nio101/MUTA_units/src/18F27J53_op_basecamp/dev_18F27J53_operator_basecamp.X/src/miwi/drv_mrf_miwi_89xa.h

/********************************************************************
 Software License Agreement:

 The software supplied herewith by Microchip Technology Incorporated
 (the "Company") for its PIC(R) Microcontroller is intended and
 supplied to you, the Company's customer, for use solely and
 exclusively on Microchip PIC Microcontroller products. The
 software is owned by the Company and/or its supplier, and is
 protected under applicable copyright laws. All rights are reserved.
 Any use in violation of the foregoing restrictions may subject the
 user to criminal sanctions under applicable laws, as well as to
 civil liability for the breach of the terms and conditions of this
 license.

 THIS SOFTWARE IS PROVIDED IN AN "AS IS" CONDITION. NO WARRANTIES,
 WHETHER EXPRESS, IMPLIED OR STATUTORY, INCLUDING, BUT NOT LIMITED
 TO, IMPLIED WARRANTIES OF MERCHANTABILITY AND FITNESS FOR A
 PARTICULAR PURPOSE APPLY TO THIS SOFTWARE. THE COMPANY SHALL NOT,
 IN ANY CIRCUMSTANCES, BE LIABLE FOR SPECIAL, INCIDENTAL OR
 CONSEQUENTIAL DAMAGES, FOR ANY REASON WHATSOEVER.
 *******************************************************************/
#ifndef _DRV_89XA_H_
#define _DRV_89XA_H_

#include "18F27J53/system.h"
#include "18F27J53/system_config.h"
#include "miwi/drv_mrf_miwi.h"
#include "miwi/drv_mrf_miwi_security.h"
#include "miwi/miwi_api.h"

/********************************************************************
MRF89XA Operating modes
**********************************************************************/
#define RF_SLEEP        0x00
#define RF_STANDBY      0x20
#define RF_SYNTHESIZER  0x40
#define RF_RECEIVER     0x60
#define RF_TRANSMITTER  0x80

#define CHIPMODE_SLEEPMODE 0x00	//000 [7:5]
#define CHIPMODE_STBYMODE  0x20	//001 ;default
#define CHIPMODE_FSMODE    0x40	//010
#define CHIPMODE_RX        0x60	//011
#define CHIPMODE_TX        0x80	//100

#define BITRATE_200     0x00
#define BITRATE_100     0x01
#define BITRATE_66      0x02
#define BITRATE_50      0x03
#define BITRATE_40      0x04
#define BITRATE_25      0x07
#define BITRATE_20      0x09
#define BITRATE_10      0x13
#define BITRATE_5       0x27
#define BITRATE_2       0x63

#define FREQBAND_902    0x00   //902-915 00 [4:3]
#define FREQBAND_915    0x08   //915-928 01 ;default
#define FREQBAND_863    0x10	//950-960 or 863-870 10

#define BW_25  0x00
#define BW_50  0x01
#define BW_75  0x02
#define BW_100 0x03
#define BW_125 0x04
#define BW_150 0x05
#define BW_175 0x06
#define BW_200 0x07
#define BW_225 0x08
#define BW_250 0x09
#define BW_275 0x0A
#define BW_300 0x0B
#define BW_325 0x0C
#define BW_350 0x0D
#define BW_375 0x0E
#define BW_400 0x0F

#define FREQ_DEV_33  0x0B
#define FREQ_DEV_40  0x09
#define FREQ_DEV_50  0x07
#define FREQ_DEV_67  0x05
#define FREQ_DEV_80  0x04
#define FREQ_DEV_100 0x03
#define FREQ_DEV_133 0x02
#define FREQ_DEV_200 0x01

#define VCO_TRIM_00 0x00            // [2:1] Vtune determined by tank inductor values
#define VCO_TRIM_01 0x02
#define VCO_TRIM_10 0x04
#define VCO_TRIM_11 0x06


#define LNA_GAIN_0_DB   0x00        //00 [1:0] 0dB ;default (This is IF Filter gain)
#define LNA_GAIN_45_DB  0x01        //01 -4.5dB
#define LNA_GAIN_9_DB   0x02        //10 -9dB
#define LNA_GAIN_135_DB 0x03        //11 -13.5dB

#define TX_POWER_13_DB      0x00    //[3:1], 13dBm
#define TX_POWER_10_DB      0x01	//10dBm
#define TX_POWER_7_DB       0x02	//7dBm
#define TX_POWER_4_DB       0x03	//4dBm
#define TX_POWER_1_DB       0x04	//1dBm
#define TX_POWER_N_2_DB     0x05	//-2dBm
#define TX_POWER_N_5_DB     0x06	//-5dBm
#define TX_POWER_N_8_DB     0x07	//-8dBm

#define FILCON_SET_65   0x00		//65 KHz
#define FILCON_SET_82   0x10		//82 KHz
#define FILCON_SET_109  0x20
#define FILCON_SET_137  0x30
#define FILCON_SET_157  0x40
#define FILCON_SET_184  0x50
#define FILCON_SET_211  0x60
#define FILCON_SET_234  0x70
#define FILCON_SET_262  0x80
#define FILCON_SET_321  0x90
#define FILCON_SET_378  0xA0
#define FILCON_SET_414  0xB0
#define FILCON_SET_458  0xC0
#define FILCON_SET_514  0xD0
#define FILCON_SET_676  0xE0
#define FILCON_SET_987  0xF0

#if defined(BAND_863)
    #define FREQ_BAND   FREQBAND_863        // 863-870 MHz or 950-960 MHz
    #if defined(APPLICATION_CIRCUIT_950)
        #define START_FREQUENCY 950000
    #else
        #define START_FREQUENCY 860000      //in KHz
    #endif
    #define R1CNT   125
    #define P1CNT	100
    #define S1CNT	20                      //center frequency - 868MHz
#elif defined(BAND_902)
    #define FREQ_BAND FREQBAND_902          // 902MHz
    #define	START_FREQUENCY 902000
    #define	R1CNT   119
    #define	P1CNT   99
    #define	S1CNT   25                        //center freq - 903MHz
#elif defined(BAND_915)
    #define FREQ_BAND   FREQBAND_915        // 915MHz
    #define	START_FREQUENCY 915000
    #define	R1CNT   119
    #define	P1CNT	100
    #define	S1CNT	50                      //center frequency - 916MHz
#else
    #error  "No valid frequency band defined"
#endif

//Define the R, P, S sets for different channels
#define	RVALUE  100

#if defined(BAND_863)
    #if(!defined(DATA_RATE_100) && !defined(DATA_RATE_200))
        #define	CHANNEL_SPACING	 300					//Channel spacing 300KHz (except for data rates 100 and 200kbps)
        #define CHANNEL_NUM 32
        #define FULL_CHANNEL_MAP 0xFFFFFFFF
    #else
        #define	CHANNEL_SPACING	384					//To support 25 channels instead of 32
        #define CHANNEL_NUM 25
        #define FULL_CHANNEL_MAP 0x01FFFFFF
    #endif
#else
    #define	CHANNEL_SPACING	 400					//Channel spacing 400KHz
    #define CHANNEL_NUM 32
    #define FULL_CHANNEL_MAP 0xFFFFFFFF
#endif

#define	FXTAL					12.8					//Frequency of the crystal in MHz

#define CHANNEL1_FREQ ((uint32_t)(START_FREQUENCY)+ CHANNEL_SPACING)
#define CHANNEL2_FREQ ((uint32_t)(START_FREQUENCY)+ (2*CHANNEL_SPACING))
#define CHANNEL3_FREQ ((uint32_t)(START_FREQUENCY)+ (3*CHANNEL_SPACING))
#define CHANNEL4_FREQ ((uint32_t)(START_FREQUENCY)+ (4*CHANNEL_SPACING))
#define CHANNEL5_FREQ ((uint32_t)(START_FREQUENCY)+ (5*CHANNEL_SPACING))
#define CHANNEL6_FREQ ((uint32_t)(START_FREQUENCY)+ (6*CHANNEL_SPACING))
#define CHANNEL7_FREQ ((uint32_t)(START_FREQUENCY)+ (7*CHANNEL_SPACING))
#define CHANNEL8_FREQ ((uint32_t)(START_FREQUENCY)+ (8*CHANNEL_SPACING))
#define CHANNEL9_FREQ ((uint32_t)(START_FREQUENCY)+ (9*CHANNEL_SPACING))
#define CHANNEL10_FREQ ((uint32_t)(START_FREQUENCY)+ (10*CHANNEL_SPACING))
#define CHANNEL11_FREQ ((uint32_t)(START_FREQUENCY)+ (11*CHANNEL_SPACING))
#define CHANNEL12_FREQ ((uint32_t)(START_FREQUENCY)+ (12*CHANNEL_SPACING))
#define CHANNEL13_FREQ ((uint32_t)(START_FREQUENCY)+ (13*CHANNEL_SPACING))
#define CHANNEL14_FREQ ((uint32_t)(START_FREQUENCY)+ (14*CHANNEL_SPACING))
#define CHANNEL15_FREQ ((uint32_t)(START_FREQUENCY)+ (15*CHANNEL_SPACING))
#define CHANNEL16_FREQ ((uint32_t)(START_FREQUENCY)+ (16*CHANNEL_SPACING))
#define CHANNEL17_FREQ ((uint32_t)(START_FREQUENCY)+ (17*CHANNEL_SPACING))
#define CHANNEL18_FREQ ((uint32_t)(START_FREQUENCY)+ (18*CHANNEL_SPACING))
#define CHANNEL19_FREQ ((uint32_t)(START_FREQUENCY)+ (19*CHANNEL_SPACING))
#define CHANNEL20_FREQ ((uint32_t)(START_FREQUENCY)+ (20*CHANNEL_SPACING))
#define CHANNEL21_FREQ ((uint32_t)(START_FREQUENCY)+ (21*CHANNEL_SPACING))
#define CHANNEL22_FREQ ((uint32_t)(START_FREQUENCY)+ (22*CHANNEL_SPACING))
#define CHANNEL23_FREQ ((uint32_t)(START_FREQUENCY)+ (23*CHANNEL_SPACING))
#define CHANNEL24_FREQ ((uint32_t)(START_FREQUENCY)+ (24*CHANNEL_SPACING))
#define CHANNEL25_FREQ ((uint32_t)(START_FREQUENCY)+ (25*CHANNEL_SPACING))
#define CHANNEL26_FREQ ((uint32_t)(START_FREQUENCY)+ (26*CHANNEL_SPACING))
#define CHANNEL27_FREQ ((uint32_t)(START_FREQUENCY)+ (27*CHANNEL_SPACING))
#define CHANNEL28_FREQ ((uint32_t)(START_FREQUENCY)+ (28*CHANNEL_SPACING))
#define CHANNEL29_FREQ ((uint32_t)(START_FREQUENCY)+ (29*CHANNEL_SPACING))
#define CHANNEL30_FREQ ((uint32_t)(START_FREQUENCY)+ (30*CHANNEL_SPACING))
#define CHANNEL31_FREQ ((uint32_t)(START_FREQUENCY)+ (31*CHANNEL_SPACING))
#define CHANNEL32_FREQ ((uint32_t)(START_FREQUENCY)+ (32*CHANNEL_SPACING))

#define CHANNEL1_COMPARE    (uint16_t)((uint32_t)(CHANNEL1_FREQ * 8 * 101)/(uint32_t)(9*FXTAL*1000))
#define CHANNEL2_COMPARE    (uint16_t)((uint32_t)(CHANNEL2_FREQ * 8 * 101)/(uint32_t)(9*FXTAL*1000))
#define CHANNEL3_COMPARE    (uint16_t)((uint32_t)(CHANNEL3_FREQ * 8 * 101)/(uint32_t)(9*FXTAL*1000))
#define CHANNEL4_COMPARE    (uint16_t)((uint32_t)(CHANNEL4_FREQ * 8 * 101)/(uint32_t)(9*FXTAL*1000))
#define CHANNEL5_COMPARE    (uint16_t)((uint32_t)(CHANNEL5_FREQ * 8 * 101)/(uint32_t)(9*FXTAL*1000))
#define CHANNEL6_COMPARE    (uint16_t)((uint32_t)(CHANNEL6_FREQ * 8 * 101)/(uint32_t)(9*FXTAL*1000))
#define CHANNEL7_COMPARE    (uint16_t)((uint32_t)(CHANNEL7_FREQ * 8 * 101)/(uint32_t)(9*FXTAL*1000))
#define CHANNEL8_COMPARE    (uint16_t)((uint32_t)(CHANNEL8_FREQ * 8 * 101)/(uint32_t)(9*FXTAL*1000))
#define CHANNEL9_COMPARE    (uint16_t)((uint32_t)(CHANNEL9_FREQ * 8 * 101)/(uint32_t)(9*FXTAL*1000))
#define CHANNEL10_COMPARE   (uint16_t)((uint32_t)(CHANNEL10_FREQ * 8 * 101)/(uint32_t)(9*FXTAL*1000))
#define CHANNEL11_COMPARE   (uint16_t)((uint32_t)(CHANNEL11_FREQ * 8 * 101)/(uint32_t)(9*FXTAL*1000))
#define CHANNEL12_COMPARE   (uint16_t)((uint32_t)(CHANNEL12_FREQ * 8 * 101)/(uint32_t)(9*FXTAL*1000))
#define CHANNEL13_COMPARE   (uint16_t)((uint32_t)(CHANNEL13_FREQ * 8 * 101)/(uint32_t)(9*FXTAL*1000))
#define CHANNEL14_COMPARE   (uint16_t)((uint32_t)(CHANNEL14_FREQ * 8 * 101)/(uint32_t)(9*FXTAL*1000))
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
#define CHANNEL26_SVALUE    (uint8_t)(((uint16_t)CHANNEL26_COMPARE - ((uint16_t)(75*(CHANNEL26_PVALUE+1)))))
#define CHANNEL27_SVALUE    (uint8_t)(((uint16_t)CHANNEL27_COMPARE - ((uint16_t)(75*(CHANNEL27_PVALUE+1)))))
#define CHANNEL28_SVALUE    (uint8_t)(((uint16_t)CHANNEL28_COMPARE - ((uint16_t)(75*(CHANNEL28_PVALUE+1)))))
#define CHANNEL29_SVALUE    (uint8_t)(((uint16_t)CHANNEL29_COMPARE - ((uint16_t)(75*(CHANNEL29_PVALUE+1)))))
#define CHANNEL30_SVALUE    (uint8_t)(((uint16_t)CHANNEL30_COMPARE - ((uint16_t)(75*(CHANNEL30_PVALUE+1)))))
#define CHANNEL31_SVALUE    (uint8_t)(((uint16_t)CHANNEL31_COMPARE - ((uint16_t)(75*(CHANNEL31_PVALUE+1)))))
#define CHANNEL32_SVALUE    (uint8_t)(((uint16_t)CHANNEL32_COMPARE - ((uint16_t)(75*(CHANNEL32_PVALUE+1)))))

#if defined(DATA_RATE_2)
    #define         DATARATE                 BITRATE_2
    #define			BANDWIDTH				 BW_50
    #define 		FREQ_DEV				 FREQ_DEV_33
    #define			FILCON_SET				 FILCON_SET_157
#elif defined(DATA_RATE_5)
    #define         DATARATE                 BITRATE_5
    #define			BANDWIDTH				 BW_50
    #define 		FREQ_DEV				 FREQ_DEV_33
    #define			FILCON_SET				 FILCON_SET_157
#elif defined(DATA_RATE_10)
    #define         DATARATE                 BITRATE_10
    #define			BANDWIDTH				 BW_50
    #define 		FREQ_DEV				 FREQ_DEV_33
    #define			FILCON_SET				 FILCON_SET_157
#elif defined(DATA_RATE_20)
    #define         DATARATE                 BITRATE_20
    #define			BANDWIDTH				 BW_75
    #define 		FREQ_DEV				 FREQ_DEV_40
    #define			FILCON_SET				 FILCON_SET_234
#elif defined(DATA_RATE_40)
    #define         DATARATE                 BITRATE_40
    #define			BANDWIDTH				 BW_150
    #define 		FREQ_DEV				 FREQ_DEV_80
    #define			FILCON_SET				 FILCON_SET_414
#elif defined(DATA_RATE_50)
    #define         DATARATE                 BITRATE_50
    #define			BANDWIDTH				 BW_175
    #define 		FREQ_DEV				 FREQ_DEV_100
    #define			FILCON_SET				 FILCON_SET_514
#elif defined(DATA_RATE_66)
    #define         DATARATE                 BITRATE_66
    #define			BANDWIDTH				 BW_250
    #define 		FREQ_DEV				 FREQ_DEV_133
    #define			FILCON_SET				 FILCON_SET_676
#elif defined(DATA_RATE_100)
    #define         DATARATE                 BITRATE_100
    #define			BANDWIDTH				 BW_400
    #define 		FREQ_DEV				 FREQ_DEV_200
    #define			FILCON_SET				 FILCON_SET_987
#elif defined(DATA_RATE_200)
    #define         DATARATE                 BITRATE_200
    #define			BANDWIDTH				 BW_400
    #define 		FREQ_DEV				 FREQ_DEV_200
    #define			FILCON_SET				 FILCON_SET_987
#endif

    //default register settings
#define GCONREG_SET     (CHIPMODE_STBYMODE | FREQ_BAND | VCO_TRIM_11)
#define DMODREG_SET     (0x84 | LNA_GAIN)
#define FLTHREG_SET     (0x0C)
#define FIFOCREG_SET    (0xC1)								//FIFO size = 64 bytes and threshold limit for IRQ is 1
#define PACONREG_SET    (0x38)
#define FTXRXIREG_SET   (0xC8)
#define FTPRIREG_SET    (0x0D)
#define RSTHIREG_SET    (0x00)	
#define FILCONREG_SET   (FILCON_SET | BANDWIDTH)
#define PFILCREG_SET    (0x38)
#define SYNCREG_SET     (0x38)
#define RESVREG_SET     (0x07)
#define SYNCV31REG_SET  (0x69)
#define SYNCV23REG_SET  (0x81)
#define SYNCV15REG_SET  (0x7E)
#define SYNCV07REG_SET  (0x96)
#define TXPARAMREG_SET  (0xF0 | (TX_POWER<<1))
#define CLKOUTREG_SET   (0x88)
#define PLOADREG_SET    (0x40)
#define NADDREG_SET     (0x00)
#define PCONREG_SET     (0xE8)
#define FCRCREG_SET     (0x00)

            //register description
#define GCONREG     0x0000
#define DMODREG     0x0200
#define FDEVREG     0x0400
#define BRREG       0x0600
#define FLTHREG     0x0800
#define FIFOCREG    0x0A00	
#define R1CNTREG    0x0C00
#define P1CNTREG    0x0E00
#define S1CNTREG    0x1000
#define R2CNTREG    0x1200
#define P2CNTREG    0x1400
#define S2CNTREG    0x1600
#define PACONREG    0x1800
#define FTXRXIREG   0x1A00
#define FTPRIREG    0x1C00
#define RSTHIREG    0x1E00
#define FILCONREG   0x2000
#define PFILCREG    0x2200
#define SYNCREG     0x2400
#define RESVREG     0x2600
#define RSTSREG     0x2800
#define OOKCREG     0x2A00
#define SYNCV31REG  0x2C00
#define SYNCV23REG  0x2E00
#define SYNCV15REG  0x3000
#define SYNCV07REG  0x3200
#define TXPARAMREG  0x3400
#define CLKOUTREG   0x3600
#define PLOADREG    0x3800
#define NADDREG     0x3A00
#define PCONREG     0x3C00
#define FCRCREG     0x3E00

#if defined(PROTOCOL_MIWI)
    #define PROTOCOL_HEADER_SIZE 11
#endif

#if defined(PROTOCOL_MIWI_PRO)
    #define PROTOCOL_HEADER_SIZE 11
#endif

#if defined(PROTOCOL_P2P)
    #define PROTOCOL_HEADER_SIZE 0
#endif

#if defined(ENABLE_SECURITY)
    #define TX_PACKET_SIZE (TX_BUFFER_SIZE+PROTOCOL_HEADER_SIZE+BLOCK_SIZE+MY_ADDRESS_LENGTH+MY_ADDRESS_LENGTH+9)
    #define RX_PACKET_SIZE (RX_BUFFER_SIZE+PROTOCOL_HEADER_SIZE+MY_ADDRESS_LENGTH+MY_ADDRESS_LENGTH+BLOCK_SIZE+9)
#else
    #define TX_PACKET_SIZE  (TX_BUFFER_SIZE+PROTOCOL_HEADER_SIZE+MY_ADDRESS_LENGTH+MY_ADDRESS_LENGTH+4)
    #define RX_PACKET_SIZE  (RX_BUFFER_SIZE+PROTOCOL_HEADER_SIZE+MY_ADDRESS_LENGTH+MY_ADDRESS_LENGTH+4)
#endif

#if RX_PACKET_SIZE > 64
    #warning  "Maximum RX PACKET SIZE should not be greater 64, redefine RX BUFFER SIZE"
    #undef RX_PACKET_SIZE
    #define RX_PACKET_SIZE 64
#endif

#if TX_PACKET_SIZE > 64
    #warning  "Maximum TX PACKET SIZE should not be greater 64, redefine TX BUFFER SIZE"
    #undef TX_PACKET_SIZE
    #define TX_PACKET_SIZE 64
#endif

typedef struct
{
    union
    {
        uint8_t    Val;
        struct
        {
            uint8_t    Valid       :1;
        } bits;
    } flags;
    uint8_t        Payload[RX_PACKET_SIZE];
    uint8_t        PayloadLen;
} RX_PACKET;

typedef struct
{
    bool        Valid;
    uint8_t        Seq;
    MIWI_TICK   startTick;
} ACK_INFO;

void MIWIInterruptHandler(void);

#endif
