nio101/MUTA_units/src/18F27J53_op_basecamp/dev_18F27J53_operator_basecamp.X/src/miwi/miwi_mesh.c

/********************************************************************
Software License Agreement:

The software supplied herewith by Microchip Technology Incorporated
(the "Company") for its PIC(R) Microcontroller is intended and
supplied to you, the Company's customer, for use solely and
exclusively on Microchip PIC Microcontroller products. The
software is owned by the Company and/or its supplier, and is
protected under applicable copyright laws. All rights are reserved.
Any use in violation of the foregoing restrictions may subject the
user to criminal sanctions under applicable laws, as well as to
civil liability for the breach of the terms and conditions of this
license.

THIS SOFTWARE IS PROVIDED IN AN "AS IS" CONDITION. NO WARRANTIES,
WHETHER EXPRESS, IMPLIED OR STATUTORY, INCLUDING, BUT NOT LIMITED
TO, IMPLIED WARRANTIES OF MERCHANTABILITY AND FITNESS FOR A
PARTICULAR PURPOSE APPLY TO THIS SOFTWARE. THE COMPANY SHALL NOT,
IN ANY CIRCUMSTANCES, BE LIABLE FOR SPECIAL, INCIDENTAL OR
CONSEQUENTIAL DAMAGES, FOR ANY REASON WHATSOEVER.
*******************************************************************/

/************************ HEADERS **********************************/

#include "system.h"
#include "system_config.h"


#include "drv_mrf_miwi.h"
#include "miwi_mesh.h"
//#include "miwi_nvm.h"
#include "miwi_api.h"

/************************ VARIABLES ********************************/

// Scan Duration formula 
//  60 * (2 ^ n + 1) symbols, where one symbol equals 16us
#define SCAN_DURATION_0 SYMBOLS_TO_TICKS(120)
#define SCAN_DURATION_1 SYMBOLS_TO_TICKS(180)
#define SCAN_DURATION_2 SYMBOLS_TO_TICKS(300)
#define SCAN_DURATION_3 SYMBOLS_TO_TICKS(540)
#define SCAN_DURATION_4 SYMBOLS_TO_TICKS(1020)
#define SCAN_DURATION_5 SYMBOLS_TO_TICKS(1980)
#define SCAN_DURATION_6 SYMBOLS_TO_TICKS(3900)
#define SCAN_DURATION_7 SYMBOLS_TO_TICKS(7740)
#define SCAN_DURATION_8 SYMBOLS_TO_TICKS(15420)
#define SCAN_DURATION_9 SYMBOLS_TO_TICKS(30780)
#define SCAN_DURATION_10 SYMBOLS_TO_TICKS(61500)
#define SCAN_DURATION_11 SYMBOLS_TO_TICKS(122940)
#define SCAN_DURATION_12 SYMBOLS_TO_TICKS(245820)
#define SCAN_DURATION_13 SYMBOLS_TO_TICKS(491580)
#define SCAN_DURATION_14 SYMBOLS_TO_TICKS(983100)
const uint32_t ScanTime[15] = {SCAN_DURATION_0,SCAN_DURATION_1,SCAN_DURATION_2,SCAN_DURATION_3,
    SCAN_DURATION_4,SCAN_DURATION_5,SCAN_DURATION_6,SCAN_DURATION_7,SCAN_DURATION_8,SCAN_DURATION_9,
    SCAN_DURATION_10, SCAN_DURATION_11, SCAN_DURATION_12, SCAN_DURATION_13,SCAN_DURATION_14
};

// permanent address definition

// MY_ADDRESS_LENGTH == 4 (always)
// and we're using the myMODEL and myUID identifiers
// as unique long address
//uint8_t myLongAddress[4] @ 0x01FFF4;
uint8_t myLongAddress[4];

/*
#if MY_ADDRESS_LENGTH == 8
    uint8_t myLongAddress[MY_ADDRESS_LENGTH] = {EUI_0,EUI_1,EUI_2,EUI_3, EUI_4, EUI_5,EUI_6,EUI_7};
#elif MY_ADDRESS_LENGTH == 7
    uint8_t myLongAddress[MY_ADDRESS_LENGTH] = {EUI_0,EUI_1,EUI_2,EUI_3, EUI_4, EUI_5,EUI_6};
#elif MY_ADDRESS_LENGTH == 6
    uint8_t myLongAddress[MY_ADDRESS_LENGTH] = {EUI_0,EUI_1,EUI_2,EUI_3, EUI_4, EUI_5};
#elif MY_ADDRESS_LENGTH == 5
    uint8_t myLongAddress[MY_ADDRESS_LENGTH] = {EUI_0,EUI_1,EUI_2,EUI_3, EUI_4};
#elif MY_ADDRESS_LENGTH == 4
    uint8_t myLongAddress[MY_ADDRESS_LENGTH] = {EUI_0,EUI_1,EUI_2,EUI_3};
#elif MY_ADDRESS_LENGTH == 3
    uint8_t myLongAddress[MY_ADDRESS_LENGTH] = {EUI_0,EUI_1,EUI_2};
#elif MY_ADDRESS_LENGTH == 2
    uint8_t myLongAddress[MY_ADDRESS_LENGTH] = {EUI_0,EUI_1};
#endif
 */

uint8_t            currentChannel = 0;             // current operating channel for the device
uint8_t            ConnMode = 0;
typedef union
{
    uint8_t        Val;
    struct
    {
        uint8_t    Sleep           :1;
        uint8_t    Role            :2;
        uint8_t    Security        :1;
        uint8_t    ConnMode        :2;
        uint8_t    CoordCap        :1;
    }bits;
} MIWI_CAPACITY_INFO;    
MIWI_CAPACITY_INFO MiWiCapacityInfo;        
RECEIVED_MESSAGE  rxMessage;                    // structure to store information for the received packet
extern uint8_t     AdditionalNodeID[];             // the additional information regarding the device
                                                // that would like to share with the peer on the
                                                // other side of P2P connection. This information
                                                // is applicaiton specific.

uint8_t    ActiveScanResultIndex;
ACTIVE_SCAN_RESULT ActiveScanResults[ACTIVE_SCAN_RESULT_SIZE];  // The results for active scan, including
                                                                // the PAN identifier, signal strength and
                                                                // operating channel

#ifdef ENABLE_SLEEP
    MIWI_TICK DataRequestTimer;
#endif

uint8_t tempLongAddress[MY_ADDRESS_LENGTH];
API_UINT16_UNION tempShortAddress;
API_UINT16_UNION tempPANID;
CONNECTION_STATUS tempNodeStatus;

uint8_t            TxData;

#if (TX_BUFFER_SIZE+MIWI_HEADER_LEN) > 110
    uint8_t TxBuffer[110];
#else
    uint8_t TxBuffer[TX_BUFFER_SIZE+MIWI_HEADER_LEN];
#endif
#if defined(ENABLE_SECURITY)
    API_UINT32_UNION IncomingFrameCounter[CONNECTION_SIZE];
#endif

API_UINT16_UNION myShortAddress;
API_UINT16_UNION myPANID;
uint8_t myParent;
uint8_t defaultHops = MAX_HOPS;

MIWI_STATE_MACHINE MiWiStateMachine;
uint8_t AcknowledgementSeq = 0xFF;
API_UINT16_UNION AcknowledgementAddr;
uint8_t MiWiSeqNum;
#if defined(ENABLE_MIWI_ACKNOWLEDGEMENT)
    bool MiWiAckRequired = true;
#else
    bool MiWiAckRequired = false;
#endif

#ifdef NWK_ROLE_COORDINATOR
    #if defined(ENABLE_INDIRECT_MESSAGE)
        #if defined(__18CXX)
            #pragma udata INDIRECT_BUFFER
        #endif
        INDIRECT_MESSAGE indirectMessages[INDIRECT_MESSAGE_SIZE];
        #if defined(__18CXX)
            #pragma udata
        #endif
    #endif
    uint8_t RoutingTable[8];
    uint8_t RouterFailures[8];
    uint8_t knownCoordinators;
    uint8_t role;
#endif

OPEN_SOCKET openSocketInfo;

MAC_TRANS_PARAM MTP;
MAC_RECEIVED_PACKET MACRxPacket;


CONNECTION_ENTRY    ConnectionTable[CONNECTION_SIZE]; 


struct _BROADCAST_RECORD
{
    API_UINT16_UNION    AltSourceAddr;
    uint8_t             MiWiSeq;
    uint8_t             RxCounter;
    MIWI_TICK           StartTick;
} BroadcastRecords[BROADCAST_RECORD_SIZE];

#if defined(ENABLE_NETWORK_FREEZER)
    MIWI_TICK nvmDelayTick;
#endif 

#if defined(ENABLE_TIME_SYNC)
    #if defined(ENABLE_SLEEP)
        API_UINT16_UNION WakeupTimes;
        API_UINT16_UNION CounterValue;
    #elif defined(ENABLE_INDIRECT_MESSAGE)
        uint8_t        TimeSyncSlot = 0;
        MIWI_TICK   TimeSyncTick;
        MIWI_TICK   TimeSlotTick;
    #endif
#endif
/************************ FUNCTIONS ********************************/

#if defined(IEEE_802_15_4)
    bool SendMACPacket(uint8_t *PANID, uint8_t *Address, uint8_t PacketType, uint8_t ModeMask);
#else
    bool SendMACPacket(uint8_t *Address, uint8_t PacketType);
#endif

bool RouteMessage(API_UINT16_UNION PANID, API_UINT16_UNION ShortAddress, bool SecEn);
void StartChannelHopping(INPUT uint8_t OptimalChannel);
void SendBeacon(void);

#if defined(IEEE_802_15_4)
    bool SaveIndirectMessage(INPUT bool Broadcast,
                             INPUT API_UINT16_UNION DestinationPANID,
                             INPUT uint8_t *DestinationAddress,
                             INPUT bool isAltAddr,
                             INPUT bool SecurityEnabled);
#else
    bool SaveIndirectMessage(INPUT bool Broadcast,
                             INPUT uint8_t *DestinationAddress,
                             INPUT bool isAltAddr,
                             INPUT bool SecurityEnabled);
#endif  

/******************************************************************/
// C18 compiler cannot optimize the code with a macro. Instead of 
// calling macro Nop in a big function, we define a wrapper to call
// Nop in order to be able to optimize the code efficiently.
/******************************************************************/
void MacroNop(void)
{
    Nop();
}   

#if !defined(TARGET_SMALL)
    /******************************************************************/
    // Function:        void BroadcastJitter(uint8_t range)
    //
    // PreCondition:    None
    //
    // Input:           range   - The range of random delay in milli
    //                            second.
    //
    // Output:          None
    //
    // Side Effect:     A random delay between 0 to range in milli
    //                  second
    //
    // Overview:        This function introduce a random delay between
    //                  0 to range in millisecond. This delay helps
    //                  multiple devices to rebroadcast the message
    //                  at different time, thus lower the possibility
    //                  of packet collision in rebroadcast.
    /******************************************************************/
    void BroadcastJitter(uint8_t range)
    {
        uint8_t jitter = TMR_L % range;
        MIWI_TICK t1, t2;

        while( jitter > 0 )
        {
            jitter--;
            t1 = MiWi_TickGet();
            while(1)
            {
                t2 = MiWi_TickGet();
                if( MiWi_TickGetDiff(t2, t1) > ONE_MILI_SECOND )
                {
                    break;
                }
            }
        }
    }
#endif

/*********************************************************************
 * Function:        void MiWiTasks( void )
 *
 * PreCondition:    None
 *
 * Input:           None
 *
 * Output:          None
 *
 * Side Effects:    The stack receives, handles, buffers, and transmits
 *                  packets.  It also handles all of the joining
 *
 * Overview:        This function maintains the operation of the stack
 *                  It should be called as often as possible.
 ********************************************************************/
void MiWiTasks(void)
{
    uint8_t i;
    MIWI_TICK t1, t2;

    if( MiMAC_ReceivedPacket() )
    {
        if( MiWiStateMachine.bits.RxHasUserData )
        {
            return;
        }

        rxMessage.flags.Val = 0;
        rxMessage.flags.bits.broadcast = MACRxPacket.flags.bits.broadcast;
        rxMessage.flags.bits.secEn = MACRxPacket.flags.bits.secEn;
        rxMessage.flags.bits.command = (MACRxPacket.flags.bits.packetType == PACKET_TYPE_COMMAND) ? 1:0;
        rxMessage.flags.bits.srcPrsnt = MACRxPacket.flags.bits.sourcePrsnt;
        if( MACRxPacket.flags.bits.sourcePrsnt )
        {
            #if defined(IEEE_802_15_4)
                rxMessage.flags.bits.altSrcAddr = MACRxPacket.altSourceAddress;
            #else
                rxMessage.flags.bits.altSrcAddr = 1;
            #endif
            rxMessage.SourceAddress = MACRxPacket.SourceAddress;
        }
        #if defined(IEEE_802_15_4)
            rxMessage.SourcePANID.Val = MACRxPacket.SourcePANID.Val;
        #endif
        rxMessage.PacketLQI = MACRxPacket.LQIValue;
        rxMessage.PacketRSSI = MACRxPacket.RSSIValue;

        MiWiStateMachine.bits.RxHasUserData = 0;

        //determine what type of packet it is.
        switch(MACRxPacket.flags.bits.packetType)
        {
            //if it is a data packet
            case PACKET_TYPE_DATA:
                //The guts of MiWi ...
                {
                    API_UINT16_UNION destPANID;
                    API_UINT16_UNION sourcePANID;
                    API_UINT16_UNION sourceShortAddress;
                    API_UINT16_UNION destShortAddress;
HANDLE_DATA_PACKET:  
                    #if defined(ENABLE_SLEEP)
                        #if defined(ENABLE_BROADCAST_TO_SLEEP_DEVICE)
                            for(i = 0; i < BROADCAST_RECORD_SIZE; i++)
                            {
                                if( BroadcastRecords[i].RxCounter > 0)
                                {
                                    BroadcastRecords[i].RxCounter--;
                                }
                            }
                        #endif

                        // If it is just an empty packet, ignore here.
                        if( MACRxPacket.PayloadLen == 0 )
                        {
                            MiWiStateMachine.bits.DataRequesting = 0;
                            break;
                        }
                    #endif

                    if( MACRxPacket.PayloadLen < 10 )
                    {
                        break;
                    }

                    // Load the source and destination address information.
                    destPANID.v[0] = MACRxPacket.Payload[2];
                    destPANID.v[1] = MACRxPacket.Payload[3];
                    destShortAddress.v[0] = MACRxPacket.Payload[4];
                    destShortAddress.v[1] = MACRxPacket.Payload[5];
                    sourcePANID.v[0] = MACRxPacket.Payload[6];
                    sourcePANID.v[1] = MACRxPacket.Payload[7];
                    sourceShortAddress.v[0] = MACRxPacket.Payload[8];
                    sourceShortAddress.v[1] = MACRxPacket.Payload[9];

                    rxMessage.flags.Val = 0;
                    rxMessage.flags.bits.secEn = MACRxPacket.flags.bits.secEn;
                    // if this is a broadcast
                    if(rxMessage.flags.bits.broadcast || destShortAddress.Val == 0xFFFF)
                    {
                        // if this broadcast is from myself
                        if( sourceShortAddress.Val == myShortAddress.Val &&
                            sourcePANID.Val == myPANID.Val )
                        {
                            break;
                        }

                        #ifdef NWK_ROLE_COORDINATOR
                            // Consider to rebroadcast the message
                            if(MACRxPacket.Payload[0]>1)
                            {
                                MACRxPacket.Payload[0]--;
                                MAC_FlushTx();
                                for(i = 0; i < MACRxPacket.PayloadLen; i++)
                                {
                                    MiApp_WriteData(MACRxPacket.Payload[i]);
                                }

                                MTP.flags.Val = MACRxPacket.flags.Val;
                                #if defined(IEEE_802_15_4)
                                    MTP.DestPANID.Val = myPANID.Val;
                                    MTP.altSrcAddr = MACRxPacket.altSourceAddress;
                                #endif

                                #if !defined(TARGET_SMALL)
                                    // introduce a random delay to avoid rebroadcast at
                                    // the same time
                                    BroadcastJitter(20);
                                #endif

                                MiMAC_SendPacket(MTP, TxBuffer, TxData);
                                #if defined(ENABLE_INDIRECT_MESSAGE)
                                    for(i = 0; i < CONNECTION_SIZE; i++)
                                    {
                                        if( ConnectionTable[i].status.bits.isValid && (ConnectionTable[i].status.bits.RXOnWhenIdle == 0) &&
                                            ConnectionTable[i].status.bits.isFamily )
                                        {
                                            break;
                                        }
                                    }
                                    if( i < CONNECTION_SIZE )
                                    {
                                        #if defined(IEEE_802_15_4)
                                            SaveIndirectMessage(true, destPANID, NULL, false, MACRxPacket.flags.bits.secEn);
                                        #else
                                            SaveIndirectMessage(true, NULL, false, MACRxPacket.flags.bits.secEn);
                                        #endif
                                    }
                                #endif
                            }
                        #endif

                        //since this is a broadcast we need to parse the packet as well.
                        for(i = 0; i < BROADCAST_RECORD_SIZE; i++)
                        {
                            if( BroadcastRecords[i].RxCounter &&
                                BroadcastRecords[i].AltSourceAddr.Val == sourceShortAddress.Val &&
                                BroadcastRecords[i].MiWiSeq == MACRxPacket.Payload[10] )
                            {
                                break;
                            }
                        }

                        // if the broadcast is already in the broadcast record
                        if( i < BROADCAST_RECORD_SIZE )
                        {
                            #if defined(ENABLE_SLEEP)
                                MiWiStateMachine.bits.DataRequesting = 0;
                            #endif
                            break;
                        }


                        // save the broadcast information into the broadcast record.
                        for(i = 0; i < BROADCAST_RECORD_SIZE; i++)
                        {
                            if( BroadcastRecords[i].RxCounter == 0 )
                            {
                                break;
                            }
                        }

                        if( i < BROADCAST_RECORD_SIZE )
                        {
                            BroadcastRecords[i].AltSourceAddr.Val = sourceShortAddress.Val;
                            BroadcastRecords[i].MiWiSeq = MACRxPacket.Payload[10];
                            BroadcastRecords[i].RxCounter = INDIRECT_MESSAGE_TIMEOUT_CYCLE + 1;
                            #if !defined(ENABLE_SLEEP)
                                BroadcastRecords[i].StartTick = MiWi_TickGet();
                            #endif
                        }

                        rxMessage.flags.bits.broadcast = 1;
                        goto ThisPacketIsForMe;
                    }

                    // this is unicast
                    if((destPANID.Val == myPANID.Val) && (destShortAddress.Val == myShortAddress.Val))
                    {
                        //need to check to see if the MiWi Ack is set
                        if(MACRxPacket.Payload[1] & MIWI_ACK_REQ)
                        {
                            TxBuffer[0] = defaultHops;				//number of hops
                            TxBuffer[1] = 0x02;		            //Frame Control
                            TxBuffer[2] = sourcePANID.v[0];
                            TxBuffer[3] = sourcePANID.v[1];
                            TxBuffer[4] = sourceShortAddress.v[0];
                            TxBuffer[5] = sourceShortAddress.v[1];
                            TxBuffer[6] = myPANID.v[0];			//source PANID LSB
                            TxBuffer[7] = myPANID.v[1];			//source PANID MSB
                            TxBuffer[8] = myShortAddress.v[0];	//source address LSB
                            TxBuffer[9] = myShortAddress.v[1];	//source address MSB
                            TxBuffer[10] = MACRxPacket.Payload[MIWI_HEADER_LEN-1];   //sequence number
                            TxBuffer[11] = MIWI_STACK_REPORT_TYPE;
                            TxBuffer[12] = ACK_REPORT_TYPE;
                            TxData = 13;

                            #if defined(NWK_ROLE_COORDINATOR)
                                if( sourceShortAddress.v[1] != myShortAddress.v[1] )
                                {
                                    RouteMessage(sourcePANID, sourceShortAddress, false);
                                }
                                else
                                {
                                    MTP.flags.Val = 0;
                                    MTP.flags.bits.ackReq = 1;

                                    #if defined(IEEE_802_15_4)
                                        MTP.altDestAddr = true;
                                        MTP.altSrcAddr = true;
                                        MTP.DestAddress = sourceShortAddress.v;
                                        MTP.DestPANID.Val = sourcePANID.Val;
                                    #else
                                        tempShortAddress.Val = sourceShortAddress.Val;
                                        tempPANID.Val = sourcePANID.Val;
                                        if( (i = SearchForShortAddress()) != 0xFF )
                                        {
                                            MTP.DestAddress = ConnectionTable[i].Address;
                                        }
                                    #endif

                                    MiMAC_SendPacket(MTP, TxBuffer, TxData);
                                }
                            #else
                                // for end device, always send the message to its parent
                                MTP.flags.Val = 0;
                                MTP.flags.bits.ackReq = 1;

                                #if defined(IEEE_802_15_4)
                                    MTP.altDestAddr = true;
                                    MTP.altSrcAddr = true;
                                    MTP.DestAddress = ConnectionTable[myParent].AltAddress.v;
                                    MTP.DestPANID.Val = myPANID.Val;
                                #else
                                    MTP.DestAddress = ConnectionTable[myParent].Address;
                                #endif

                                MiMAC_SendPacket(MTP, TxBuffer, TxData);
                            #endif
                            rxMessage.flags.bits.ackReq = 1;
                        }

ThisPacketIsForMe:
                        //if the packet is a MiWi stack packet (but not an ACK report type
                        if(MACRxPacket.Payload[MIWI_HEADER_LEN] == MIWI_STACK_REPORT_TYPE)
                        {
                            if( MACRxPacket.Payload[MIWI_HEADER_LEN+1] != ACK_REPORT_TYPE)
                            {
                                //determine which stack report it was
                                switch(MACRxPacket.Payload[MIWI_HEADER_LEN+1])
                                {
                                    #if defined(SUPPORT_EUI_ADDRESS_SEARCH)
                                    #if defined(NWK_ROLE_COORDINATOR)
                                    case EUI_ADDRESS_SEARCH_REQUEST:
                                        {
                                            uint8_t handle,j;
                                            bool ItsMe;

                                            if(sourceShortAddress.Val == myShortAddress.Val)
                                            {
                                                if(sourcePANID.Val == myPANID.Val)
                                                {
                                                    //I started this message.  I don't need to re-broadcast it.
                                                    break;
                                                }
                                            }

                                            //copy the address into tempLongAddress
                                            CONSOLE_PutString((char*)"\r\nEUI address search request\r\n");
                                            for(j = 0; j < MY_ADDRESS_LENGTH; j++)
                                            {
                                                tempLongAddress[j] = MACRxPacket.Payload[MIWI_HEADER_LEN+2+j];
                                            }


                                            ItsMe = true;
                                            for(j=0;j<MY_ADDRESS_LENGTH;j++)
                                            {
                                                //see if the address in question is my own
                                                if(tempLongAddress[j] != myLongAddress[j])
                                                {
                                                    ItsMe = false;
                                                    break;
                                                }
                                            }

                                            //load up the TX Buffer with the results
                                            MiApp_FlushTx();
                                            MiApp_WriteData(MIWI_STACK_REPORT_TYPE);      //Report Type
                                            MiApp_WriteData(EUI_ADDRESS_SEARCH_RESPONSE);      //Report ID
                                            for(j = 0; j < MY_ADDRESS_LENGTH; j++)
                                            {
                                                MiApp_WriteData(tempLongAddress[j]);      //Data byte 0
                                            }

                                            //if it wasn't me
                                            if(ItsMe == false)
                                            {
                                                //search the network table for the device
                                                handle = SearchForLongAddress();

                                                //if we found the device
                                                if(handle!=0xFF)
                                                {
                                                    //check to see if the short address is valid for that device
                                                    if(networkStatus[handle].bits.shortAddressValid)
                                                    {
                                                        //I know the device in question so I will send back a response
                                                        MiApp_WriteData(networkTable[handle].PANID.v[0]);
                                                        MiApp_WriteData(networkTable[handle].PANID.v[1]);
                                                        MiApp_WriteData(networkTable[handle].AltAddress.v[0]);
                                                        MiApp_WriteData(networkTable[handle].AltAddress.v[1]);

                                                        //if everything is cool then send the response back
                                                        RouteMessage(sourcePANID, sourceShortAddress, false);
                                                        //SendReportByShortAddress(sourcePANID,sourceShortAddress, false);
                                                    }
                                                    else
                                                    {
                                                        //if we didn't have the short address then we can't
                                                        //respond to this packet even though we know the long address
                                                        CONSOLE_PutString((char*)"found long address but short address not valid\r\n");
                                                        //clear out the data I already wrote
                                                        TxData = 0;
                                                    }

                                                }
                                                else
                                                {
                                                    //if we couldn't find the long address of the device then forget it
                                                    CONSOLE_PutString((char*)"couldn't find the device");
                                                    TxData = 0;
                                                }
                                            }
                                            else
                                            {
                                                //The node in question is me
                                                TxBuffer[TxData++] = myPANID.v[0];
                                                TxBuffer[TxData++] = myPANID.v[1];
                                                TxBuffer[TxData++] = myShortAddress.v[0];
                                                TxBuffer[TxData++] = myShortAddress.v[1];

                                                //send a response back with my own information
                                                RouteMessage(sourcePANID, sourceShortAddress, false);
                                            }
                                        }
                                        break;
                                    #endif //COORDINATOR_CAPABLE
                                    #endif //SUPPORT_EUI_ADDRESS_SEARCH


                                    #if defined(SUPPORT_EUI_ADDRESS_SEARCH)
                                    case EUI_ADDRESS_SEARCH_RESPONSE:
                                        {
                                            //got a response back from the IEEE address search
                                            //record all of the information in the packet
                                            //long address

                                            MiWiStateMachine.bits.EUISearching = 0;
                                            for(i = 0; i < MY_ADDRESS_LENGTH; i++)
                                            {
                                                tempLongAddress[i] = MACRxPacket.Payload[MIWI_HEADER_LEN+2+i];
                                            }
                                            //PANID and short address
                                            tempPANID.v[0] = MACRxPacket.Payload[MIWI_HEADER_LEN+2+MY_ADDRESS_LENGTH];
                                            tempPANID.v[1] = MACRxPacket.Payload[MIWI_HEADER_LEN+3+MY_ADDRESS_LENGTH];
                                            tempShortAddress.v[0] = MACRxPacket.Payload[MIWI_HEADER_LEN+4+MY_ADDRESS_LENGTH];
                                            tempShortAddress.v[1] = MACRxPacket.Payload[MIWI_HEADER_LEN+5+MY_ADDRESS_LENGTH];

                                            if( (SearchForLongAddress() == 0xFF) && (SearchForShortAddress() == 0xFF ) )
                                            {
                                                //create a new Status entry for the network table
                                                tempNodeStatus.Val = 0x8D;
                                                if( tempShortAddress.v[0] & 0x80 )
                                                {
                                                    tempNodeStatus.bits.RXOnWhenIdle = 0;
                                                }
                                                if((tempShortAddress.Val == sourceShortAddress.Val)
                                                    #if defined(IEEE_802_15_4)
                                                        && (tempPANID.Val == sourcePANID.Val)
                                                    #endif
                                                   )
                                                {
                                                    tempNodeStatus.bits.directConnection = 1;
                                                }
                                                //add the node to the network table
                                                i = AddNodeToNetworkTable();
                                                #if defined(ENABLE_NETWORK_FREEZER)
                                                    if( i < 0xFF )
                                                    {
                                                        nvmPutConnectionTableIndex(&(ConnectionTable[i]), i);
                                                    }
                                                #endif
                                            }
                                        }
                                        break;
                                    #endif

                                    #ifdef NWK_ROLE_COORDINATOR
                                    case OPEN_SOCKET_REQUEST:
                                        {
                                            uint8_t j;

                                            //if we have a socket request open
                                            if(openSocketInfo.status.bits.requestIsOpen == 0)
                                            {
                                                //if there isn't a request already open
                                                //get the current time and the source address
                                                openSocketInfo.socketStart = MiWi_TickGet();
                                                openSocketInfo.ShortAddress1.v[0] = MACRxPacket.Payload[MIWI_HEADER_LEN-3];
                                                openSocketInfo.ShortAddress1.v[1] = MACRxPacket.Payload[MIWI_HEADER_LEN-2];

                                                //copy the long address
                                                for(j=0;j<MY_ADDRESS_LENGTH;j++)
                                                {
                                                    openSocketInfo.LongAddress1[j] = MACRxPacket.Payload[j+2+MIWI_HEADER_LEN];
                                                }
                                                //mark a request as open
                                                openSocketInfo.status.bits.requestIsOpen = 1;
                                                openSocketInfo.status.bits.matchFound = 0;

                                                #if ADDITIONAL_NODE_ID_SIZE > 0
                                                    for(j = 0; j < ADDITIONAL_NODE_ID_SIZE; j++)
                                                    {
                                                        openSocketInfo.AdditionalNodeID1[j] = MACRxPacket.Payload[MIWI_HEADER_LEN+2+MY_ADDRESS_LENGTH+j];
                                                    }
                                                #endif
                                            }
                                            else
                                            {
                                                //if there was already a request open

                                                if( (MACRxPacket.Payload[MIWI_HEADER_LEN-3] == openSocketInfo.ShortAddress1.v[0]) &&
                                                    (MACRxPacket.Payload[MIWI_HEADER_LEN-2] == openSocketInfo.ShortAddress1.v[1]))
                                                {
                                                    //if we get a request from the same guy twice,
                                                    //just throw away the second request
                                                    //CONSOLE_PutString((char*)"got request from same guy twice\r\n");
                                                }
                                                else if(openSocketInfo.ShortAddress1.Val == 0x0000)
                                                {
                                                    //I am the PAN coordinator and I initiated the request so don't send back a response to myself
                                                    //copy the long and short address from the Rx Buffer
                                                    for(j=0;j<MY_ADDRESS_LENGTH;j++)
                                                    {
                                                        openSocketInfo.LongAddress2[j] = MACRxPacket.Payload[MIWI_HEADER_LEN+2+j];      //Data byte
                                                        tempLongAddress[j] = openSocketInfo.LongAddress2[j];
                                                    }

                                                    //save the important information about the node sending
                                                    //the request
                                                    openSocketInfo.ShortAddress2.v[0] = MACRxPacket.Payload[MIWI_HEADER_LEN-3];
                                                    openSocketInfo.ShortAddress2.v[1] = MACRxPacket.Payload[MIWI_HEADER_LEN-2];

                                                    tempShortAddress.v[0] = openSocketInfo.ShortAddress2.v[0];
                                                    tempShortAddress.v[1] = openSocketInfo.ShortAddress2.v[1];
                                                    tempPANID.Val = myPANID.Val;

                                                    //look to see if that device exists in our network table
                                                    openSocketInfo.socketHandle = SearchForShortAddress();

                                                    if(openSocketInfo.socketHandle == 0xFF)
                                                    {
                                                        //otherwise create it
                                                        //Family, RxOnWHenIdle, Neighbor/Network, P2P, ShortVal, LongVal, Direct, Valid
                                                        tempNodeStatus.Val = 0x8D;
                                                        if(tempShortAddress.v[0] & 0x80)
                                                        {
                                                            tempNodeStatus.bits.RXOnWhenIdle = 0;
                                                        }

                                                        openSocketInfo.socketHandle = AddNodeToNetworkTable();
                                                        if( openSocketInfo.socketHandle < 0xFF )
                                                        {
                                                            #if ADDITIONAL_NODE_ID_SIZE > 0
                                                                for(j = 0; j < ADDITIONAL_NODE_ID_SIZE; j++)
                                                                {
                                                                    ConnectionTable[openSocketInfo.socketHandle].PeerInfo[j] = MACRxPacket.Payload[MIWI_HEADER_LEN+2+MY_ADDRESS_LENGTH+j];
                                                                }
                                                            #endif
                                                            #if defined(ENABLE_NETWORK_FREEZER)
                                                                nvmPutConnectionTableIndex(&(ConnectionTable[openSocketInfo.socketHandle]), openSocketInfo.socketHandle);
                                                            #endif
                                                        }
                                                    }


                                                    openSocketInfo.status.bits.requestIsOpen = 1;
                                                    openSocketInfo.status.bits.matchFound = 1;
                                                }
                                                else
                                                {
                                                    CONSOLE_PutString((char*)"sending out response\r\n");

                                                    //we got a match so let's send out the response

                                                    MiApp_FlushTx();
                                                    MiApp_WriteData(MIWI_STACK_REPORT_TYPE);          //Report Type
                                                    MiApp_WriteData(OPEN_SOCKET_RESPONSE);    //Report ID

                                                    //copy the long and short address from the Rx Buffer
                                                    for(j=0;j<MY_ADDRESS_LENGTH;j++)
                                                    {
                                                        openSocketInfo.LongAddress2[j] = MACRxPacket.Payload[MIWI_HEADER_LEN+2+j];      //Data byte
                                                        MiApp_WriteData(openSocketInfo.LongAddress2[j]);
                                                    }

                                                    openSocketInfo.ShortAddress2.v[0] = MACRxPacket.Payload[MIWI_HEADER_LEN-3];
                                                    openSocketInfo.ShortAddress2.v[1] = MACRxPacket.Payload[MIWI_HEADER_LEN-2];
                                                    /*#if ADDITIONAL_NODE_ID_SIZE > 0
                                                        for(j = 0; j < ADDITIONAL_NODE_ID_SIZE; j++)
                                                        {
                                                            openSocketInfo.AdditionalNodeID2[j] = MACRxPacket.Payload[MIWI_HEADER_LEN+10+j];
                                                        }
                                                    #endif
                                                    */

                                                    MiApp_WriteData(openSocketInfo.ShortAddress2.v[0]);
                                                    MiApp_WriteData(openSocketInfo.ShortAddress2.v[1]);
                                                    #if ADDITIONAL_NODE_ID_SIZE > 0
                                                        for(j = 0; j < ADDITIONAL_NODE_ID_SIZE; j++)
                                                        {
                                                            MiApp_WriteData(MACRxPacket.Payload[MIWI_HEADER_LEN+2+MY_ADDRESS_LENGTH+j]);
                                                        }
                                                    #endif


                                                    //MiApp_UnicastAddress(openSocketInfo.ShortAddress1.v, false, false);
                                                        UnicastShortAddress(openSocketInfo.ShortAddress1.v);
                                                    openSocketInfo.status.bits.requestIsOpen = 1;
                                                    openSocketInfo.status.bits.matchFound = 1;
                                                }

                                            }
                                        }
                                        break;
                                    #endif

                                    case OPEN_SOCKET_RESPONSE:
                                        {
                                            uint8_t j;

                                            //save the long address of the device
                                            for(j=0;j<MY_ADDRESS_LENGTH;j++)
                                            {
                                                tempLongAddress[j] = MACRxPacket.Payload[j+13];
                                            }

                                            //create a new status for the device
                                            tempNodeStatus.Val = 0x8D;
                                            //check the RxOnWhenIdle bit
                                            if(MACRxPacket.Payload[13+MY_ADDRESS_LENGTH] & 0x80)
                                            {
                                                tempNodeStatus.bits.RXOnWhenIdle = 0;
                                            }

                                            //copy the short address
                                            tempShortAddress.v[0] = MACRxPacket.Payload[MY_ADDRESS_LENGTH+13];
                                            tempShortAddress.v[1] = MACRxPacket.Payload[MY_ADDRESS_LENGTH+14];

                                            //use my PANID since this version of MiWi only supports single PANIDs
                                            tempPANID.Val = myPANID.Val;

                                            //see if this node already exists in my table
                                            openSocketInfo.socketHandle = SearchForShortAddress();

                                            if(openSocketInfo.socketHandle != 0xFF)
                                            {
                                                //if it does then get the status of the node already in the table
                                                tempNodeStatus.Val = ConnectionTable[openSocketInfo.socketHandle].status.Val;
                                                tempNodeStatus.bits.longAddressValid = 1;
                                                tempNodeStatus.bits.shortAddressValid = 1;
                                            }
                                            else
                                            {
                                                //Family, RxOnWHenIdle, Neighbor/Network, P2P, ShortVal, LongVal, Direct, Valid
                                                tempNodeStatus.Val = 0x8D;
                                                if(tempShortAddress.v[0] & 0x80)
                                                {
                                                    tempNodeStatus.bits.RXOnWhenIdle = 0;
                                                }
                                            }
                                            //update the network information
                                            openSocketInfo.socketHandle = AddNodeToNetworkTable();
                                            if( openSocketInfo.socketHandle < 0xFF )
                                            {
                                                #if ADDITIONAL_NODE_ID_SIZE > 0
                                                    for(j = 0; j < ADDITIONAL_NODE_ID_SIZE; j++)
                                                    {
                                                        ConnectionTable[openSocketInfo.socketHandle].PeerInfo[j] = MACRxPacket.Payload[MY_ADDRESS_LENGTH+4+MIWI_HEADER_LEN+j];
                                                    }
                                                #endif
                                                #if defined(ENABLE_NETWORK_FREEZER)
                                                    nvmPutConnectionTableIndex(&(ConnectionTable[openSocketInfo.socketHandle]), openSocketInfo.socketHandle);
                                                #endif
                                                openSocketInfo.status.bits.matchFound = 1;
                                            }
                                            else
                                            {
                                                openSocketInfo.status.bits.matchFound = 0;
                                            }

                                            //clear out out request
                                            openSocketInfo.status.bits.requestIsOpen = 0;

                                        }
                                        break;


                                    #if defined(ENABLE_FREQUENCY_AGILITY)

                                            case CHANNEL_HOPPING_REQUEST:
                                                {
                                                    if( MACRxPacket.Payload[MIWI_HEADER_LEN+2] != currentChannel )
                                                    {
                                                        break;
                                                    }
                                                    MiApp_SetChannel(MACRxPacket.Payload[MIWI_HEADER_LEN+3]);
                                                    Printf("\r\nHopping Channel to ");
                                                    CONSOLE_PrintDec(currentChannel);
                                                }
                                                break;

                                       #if defined(NWK_ROLE_COORDINATOR)
                                            case RESYNCHRONIZATION_REQUEST:
                                                {
                                                    if( MACRxPacket.Payload[MIWI_HEADER_LEN+2] != currentChannel )
                                                    {
                                                        break;
                                                    }
                                                    MAC_FlushTx();
                                                    TxBuffer[0] = defaultHops;
                                                    TxBuffer[1] = 0x02;
                                                    TxBuffer[2] = myPANID.v[0];
                                                    TxBuffer[3] = myPANID.v[1];
                                                    TxBuffer[4] = MACRxPacket.Payload[8];
                                                    TxBuffer[5] = MACRxPacket.Payload[9];
                                                    TxBuffer[6] = myPANID.v[0];
                                                    TxBuffer[7] = myPANID.v[1];
                                                    TxBuffer[8] = myShortAddress.v[0];
                                                    TxBuffer[9] = myShortAddress.v[1];
                                                    TxBuffer[10] = MiWiSeqNum++;
                                                    TxBuffer[11] = MIWI_STACK_REPORT_TYPE;
                                                    TxBuffer[12] = RESYNCHRONIZATION_RESPONSE;

                                                    MTP.flags.Val = 0;
                                                    MTP.flags.bits.ackReq = 1;
                                                    #if defined(IEEE_802_15_4)
                                                        MTP.altDestAddr = true;
                                                        MTP.altSrcAddr = true;
                                                        MTP.DestPANID.Val = myPANID.Val;
                                                        MTP.DestAddress = &(MACRxPacket.Payload[8]);
                                                    #else
                                                        tempShortAddress.v[0] = MACRxPacket.Payload[8];
                                                        tempShortAddress.v[1] = MACRxPacket.Payload[9];
                                                        i = SearchForShortAddress();
                                                        if( i == 0xFF )
                                                        {
                                                            break;
                                                        }
                                                        MTP.DestAddress = ConnectionTable[i].Address;
                                                    #endif

                                                    MiMAC_SendPacket(MTP, TxBuffer, 13);
                                                }
                                                break;
                                        #endif

                                        case RESYNCHRONIZATION_RESPONSE:
                                            {
                                                MiWiStateMachine.bits.Resynning = 0;
                                            }
                                            break;


                                    #endif

                                    default:
                                        //unknown stack request.  don't do anything
                                        //just let this packet die
                                        break;
                                }
                            }
                            else
                            {
                                // in case receive acknowledgement
                                if( AcknowledgementSeq == MACRxPacket.Payload[MIWI_HEADER_LEN-1] &&
                                    sourceShortAddress.Val == AcknowledgementAddr.Val)
                                {
                                    MiWiStateMachine.bits.MiWiAckInProgress = 0;
                                }

                                break;
                            }
                        }
                        else
                        {
                            //This data is for the user, pass it up to them
                            #if defined(ENABLE_SLEEP)
                                MiWiStateMachine.bits.DataRequesting = 0;
                            #endif
                            rxMessage.PayloadSize = MACRxPacket.PayloadLen - 11;
                            rxMessage.Payload = &MACRxPacket.Payload[11];
                            rxMessage.SourcePANID.Val = sourcePANID.Val;
                            if( MACRxPacket.Payload[8] == 0xFF && MACRxPacket.Payload[9] == 0xFF )
                            {
                                #if defined(IEEE_802_15_4)
                                    rxMessage.flags.bits.altSrcAddr = MACRxPacket.altSourceAddress;
                                    rxMessage.SourceAddress = MACRxPacket.SourceAddress;
                                #else
                                    if( MACRxPacket.flags.bits.sourcePrsnt )
                                    {
                                        rxMessage.SourceAddress = MACRxPacket.SourceAddress;
                                    }
                                    else
                                    {
                                        rxMessage.flags.bits.altSrcAddr = 1;
                                        rxMessage.SourceAddress = &(MACRxPacket.Payload[8]);
                                    }
                                #endif

                            }
                            else
                            {
                                rxMessage.flags.bits.altSrcAddr = 1;
                                rxMessage.SourceAddress = &(MACRxPacket.Payload[8]);
                            }
                            rxMessage.flags.bits.srcPrsnt = 1;

                            if( rxMessage.PayloadSize > 0 )
                            {
                                MiWiStateMachine.bits.RxHasUserData = 1;
                            }

                        }
                    }
                    else
                    {
                        //if this packet wasn't for me
                        #ifdef NWK_ROLE_COORDINATOR
                            //then if I am a coordinator pass it along to the
                            //next hop, decrementing the number of hops available
                            if( MACRxPacket.Payload[0] > 0 )
                            {
                                MACRxPacket.Payload[0]--;      //decrement the hops counter
                                MAC_FlushTx();
                                for(i = 0; i < MACRxPacket.PayloadLen; i++)
                                {
                                    MiApp_WriteData(MACRxPacket.Payload[i]);
                                }

                                if( (destShortAddress.v[1] == myShortAddress.v[1]) &&
                                    (TxBuffer[11] == MIWI_STACK_REPORT_TYPE) &&
                                    (TxBuffer[12] == ACK_REPORT_TYPE) )
                                {
                                    MTP.flags.Val = 0;
                                    MTP.flags.bits.ackReq = 1;

                                    #if defined(IEEE_802_15_4)
                                        MTP.altDestAddr = true;
                                        MTP.altSrcAddr = true;
                                        MTP.DestAddress = destShortAddress.v;
                                        MTP.DestPANID.Val = destPANID.Val;
                                        MiMAC_SendPacket(MTP, TxBuffer, TxData);
                                    #else
                                        tempShortAddress.Val = destShortAddress.Val;
                                        if( (i = SearchForShortAddress()) != 0xFF )
                                        {
                                            MTP.DestAddress = ConnectionTable[i].Address;
                                            MiMAC_SendPacket(MTP, TxBuffer, TxData);
                                        }
                                    #endif
                                }
                                else
                                {
                                    RouteMessage(destPANID, destShortAddress, MACRxPacket.flags.bits.secEn);
                                }
                            }
                        #endif
                    }

                }
                break;

            //if it is a beacon packet
            case PACKET_TYPE_BEACON:
                {
                    uint8_t rxIndex;

                    #if defined(IEEE_802_15_4)
                        rxIndex = 0;
                    #else
                        rxIndex = 4;
                    #endif


                    if(MACRxPacket.Payload[rxIndex+4] != MIWI_PROTOCOL_ID )
                    {
                        #if defined(NWK_ROLE_END_DEVICE)
                            if(MACRxPacket.Payload[rxIndex+4] != MIWI_PRO_PROTOCOL_ID)
                        #endif
                        {
                            break;
                        }
                    }

                    #ifdef NWK_ROLE_COORDINATOR
                    {
                        //if I am a coordinator then get
                        //the coordinators number
                        #if defined(IEEE_802_15_4)
                            uint8_t coordinatorNumber = MACRxPacket.SourceAddress[1];
                        #else
                            uint8_t coordinatorNumber = MACRxPacket.Payload[3];
                        #endif
                        uint8_t mask = 1<<(coordinatorNumber);

                        //Make sure its a MiWi coordinator
                        #if defined(IEEE_802_15_4)
                            if( MACRxPacket.SourceAddress[0]== 0x00 )
                        #else
                            if(MACRxPacket.Payload[2] == 0x00)
                        #endif
                        {
                            //if it is then mark this device as known
                            knownCoordinators |= mask;
                        }

                        RoutingTable[coordinatorNumber] = MACRxPacket.Payload[rxIndex+6];
                        #if defined(ENABLE_NETWORK_FREEZER)
                            MiWiStateMachine.bits.saveConnection = 1;
                        #endif
                    }
                    #endif

                    #if !defined(IEEE_802_15_4) && defined(NWK_ROLE_COORDINATOR)
                        {
                            uint8_t entry;

                            tempPANID.v[0] = MACRxPacket.Payload[0];
                            tempPANID.v[1] = MACRxPacket.Payload[1];
                            tempShortAddress.v[0] = MACRxPacket.Payload[2];
                            tempShortAddress.v[1] = MACRxPacket.Payload[3];

                            entry = SearchForShortAddress();
                            if(entry == 0xFF)
                            {
                                //this device doesn't already exist in our network table
                                //let's create a new entry for it.
                                entry = findNextNetworkEntry();
                            }
                            else
                            {
                                for(i = 0; i < MY_ADDRESS_LENGTH; i++)
                                {
                                    if( ConnectionTable[entry].Address[i] != MACRxPacket.SourceAddress[i] )
                                    {
                                        break;
                                    }
                                }
                                if( i >= MY_ADDRESS_LENGTH )
                                {
                                    entry = 0xFF;
                                }
                            }

                            if( entry < 0xFF )
                            {
                                ConnectionTable[entry].PANID.Val = tempPANID.Val;
                                ConnectionTable[entry].AltAddress.Val = tempShortAddress.Val;

                                for(i = 0; i < MY_ADDRESS_LENGTH; i++)
                                {
                                    ConnectionTable[entry].Address[i] = MACRxPacket.SourceAddress[i];
                                }

                                //mark this as a valid entry
                                ConnectionTable[entry].status.Val = 0;
                                ConnectionTable[entry].status.bits.directConnection = 1;
                                ConnectionTable[entry].status.bits.RXOnWhenIdle = 1;
                                ConnectionTable[entry].status.bits.longAddressValid = 1;
                                ConnectionTable[entry].status.bits.shortAddressValid = 1;
                                ConnectionTable[entry].status.bits.isValid = 1;

                                #if defined(ENABLE_NETWORK_FREEZER)
                                    MiWiStateMachine.bits.saveConnection = 1;
                                #endif
                            }
                        }
                    #endif

                    #if defined(ENABLE_NETWORK_FREEZER)
                        if( MiWiStateMachine.bits.saveConnection == 1 )
                        {
                            nvmDelayTick = MiWi_TickGet();
                        }
                    #endif

                    //if we are looking for a network
                    if(MiWiStateMachine.bits.searchingForNetwork)
                    {
                        #if defined(IEEE_802_15_4)
                            tempPANID.Val = MACRxPacket.SourcePANID.Val;
                            tempShortAddress.v[0] = MACRxPacket.SourceAddress[0];
                            tempShortAddress.v[1] = MACRxPacket.SourceAddress[1];
                        #else
                            tempPANID.v[0] = MACRxPacket.Payload[0];
                            tempPANID.v[1] = MACRxPacket.Payload[1];
                            tempShortAddress.v[0] = MACRxPacket.Payload[2];
                            tempShortAddress.v[1] = MACRxPacket.Payload[3];
                        #endif

                        //ignore all beacon networks
                        if(MACRxPacket.Payload[rxIndex] == 0xFF)
                        {
                            MIWI_CAPACITY_INFO CapacityByte;
                            CapacityByte.Val = MACRxPacket.Payload[rxIndex+1];
                            if( (ActiveScanResultIndex < ACTIVE_SCAN_RESULT_SIZE) && (CapacityByte.bits.ConnMode <= ENABLE_PREV_CONN) )
                            {

                                ActiveScanResults[ActiveScanResultIndex].Channel = currentChannel;
                                ActiveScanResults[ActiveScanResultIndex].RSSIValue = rxMessage.PacketRSSI;
                                ActiveScanResults[ActiveScanResultIndex].LQIValue = rxMessage.PacketLQI;
                                ActiveScanResults[ActiveScanResultIndex].PANID.Val = tempPANID.Val;

                                ActiveScanResults[ActiveScanResultIndex].Capability.Val = 0;
                                ActiveScanResults[ActiveScanResultIndex].Capability.bits.Direct = 1;
                                ActiveScanResults[ActiveScanResultIndex].Capability.bits.Role = CapacityByte.bits.Role;
                                if( CapacityByte.bits.Security )
                                {
                                    ActiveScanResults[ActiveScanResultIndex].Capability.bits.SecurityEn = 1;
                                }
                                if( CapacityByte.bits.ConnMode <= ENABLE_PREV_CONN )
                                {
                                    ActiveScanResults[ActiveScanResultIndex].Capability.bits.AllowJoin = 1;
                                }


                                #if defined(IEEE_802_15_4)
                                    ActiveScanResults[ActiveScanResultIndex].Address[0] = rxMessage.SourceAddress[0];
                                    ActiveScanResults[ActiveScanResultIndex].Address[1] = rxMessage.SourceAddress[1];
                                    ActiveScanResults[ActiveScanResultIndex].Capability.bits.altSrcAddr = 1;
                                #else
                                    for(i = 0; i < MY_ADDRESS_LENGTH; i++)
                                    {
                                        ActiveScanResults[ActiveScanResultIndex].Address[i] = rxMessage.SourceAddress[i];
                                    }
                                #endif
                                #if ADDITIONAL_NODE_ID_SIZE > 0
                                    for(i = 0; i < ADDITIONAL_NODE_ID_SIZE; i++)
                                    {
                                        ActiveScanResults[ActiveScanResultIndex].PeerInfo[i] = MACRxPacket.Payload[rxIndex+7+i];
                                    }
                                #endif
                                ActiveScanResultIndex++;
                            }
                        }
                    }
                }
                break;


            //if it is a command packet
            case PACKET_TYPE_COMMAND:
HANDLE_COMMAND_PACKET:
                //figure out which command packet it is
                switch(MACRxPacket.Payload[0])
                {
                    #ifdef NWK_ROLE_COORDINATOR
                    case MAC_COMMAND_ASSOCIATION_REQUEST:
                        {
                            uint8_t handle;
                            uint8_t associateStatus = ASSOCIATION_SUCCESSFUL;

                            if( ConnMode > ENABLE_PREV_CONN )
                            {
                                break;
                            }

                            //get the long address of the device
                            for(i = 0; i < MY_ADDRESS_LENGTH; i++)
                            {
                                tempLongAddress[i] = MACRxPacket.SourceAddress[i];
                            }

                            handle = SearchForLongAddress();
                            if( handle == 0xFF )
                            {
                                if( ConnMode > ENABLE_ALL_CONN )
                                {
                                    break;
                                }
                                tempNodeStatus.Val = 0xB7;
                                tempPANID.Val = myPANID.Val;

                                //add this node to the network table
                                handle = AddNodeToNetworkTable();
                                if( handle == 0xFF )
                                {
                                    associateStatus = ASSOCIATION_PAN_FULL;
                                    tempShortAddress.Val = 0xFFFE;
                                    goto START_ASSOCIATION_RESPONSE;
                                }
                                #if defined(ENABLE_NETWORK_FREEZER)
                                    nvmPutConnectionTableIndex(&(ConnectionTable[handle]), handle);
                                #endif
                            }
                            else
                            {
                                if( ConnectionTable[handle].status.bits.shortAddressValid )
                                {
                                    tempShortAddress.Val = ConnectionTable[handle].AltAddress.Val;
                                    goto START_ASSOCIATION_RESPONSE;
                                }
                            }

                            //if entry was successful then assign the device a short address
                            if(handle != 0xFF)
                            {
                                //set the short address as an end device address
                                tempShortAddress.v[0] = handle + 1;
                                tempShortAddress.v[1] = myShortAddress.v[1];
                                tempPANID.Val = myPANID.Val;

                                //if I am the PAN coordinator
                                if(role == ROLE_PAN_COORDINATOR)
                                {
                                    if(MACRxPacket.Payload[1] & 0x40)
                                    {
                                        //If this device is a potential coordinator
                                        uint8_t j;
                                        API_UINT16_UNION CoordAddress;
                                        uint8_t entry;

                                        CoordAddress.Val = tempShortAddress.Val;
                                        tempShortAddress.v[0] = 0;

                                        //search to see if there is a coordinator address available
                                        for(j=1;j<8;j++)
                                        {
                                            tempShortAddress.v[1] = j;
                                            entry = SearchForShortAddress();

                                            if(entry == 0xFF)
                                            {
                                                tempShortAddress.v[0] = 0x00;
                                                tempShortAddress.v[1] = j;
                                                knownCoordinators |= (1<<j);
                                                #if defined(ENABLE_NETWORK_FREEZER)
                                                    nvmPutKnownCoordinators(&knownCoordinators);
                                                #endif
                                                break;
                                            }
                                        }

                                        if(j==8)
                                        {
                                            tempShortAddress.Val= CoordAddress.Val;
                                        }

                                    }
                                }

                                //create a new status entry for the device
                                tempNodeStatus.Val = 0xBF;

                                //mark if the Rx is on when idle
                                if((MACRxPacket.Payload[1] & 0x01) == 0)
                                {
                                    tempNodeStatus.bits.RXOnWhenIdle = 0;
                                    tempShortAddress.v[0] |= 0x80;
                                }

                                //update the information in the network table
                                handle = AddNodeToNetworkTable();

                                ConnectionTable[handle].status.bits.FinishJoin = 1;

                                #if ADDITIONAL_NODE_ID_SIZE > 0
                                    for(i = 0; i < ADDITIONAL_NODE_ID_SIZE; i++)
                                    {
                                        ConnectionTable[handle].PeerInfo[i] = MACRxPacket.Payload[2+i];
                                    }
                                #endif


                                if( MiApp_CB_AllowConnection(handle) == false )
                                {
                                    ConnectionTable[handle].status.Val = 0;
                                    associateStatus = ASSOCIATION_ACCESS_DENIED;
                                }

                                #if defined(ENABLE_NETWORK_FREEZER)
                                    nvmPutConnectionTableIndex(&(ConnectionTable[handle]), handle);
                                #endif
                            }

START_ASSOCIATION_RESPONSE:                          
                            //send back the asociation response
                            TxBuffer[0] = MAC_COMMAND_ASSOCIATION_RESPONSE;
                            TxBuffer[1] = tempShortAddress.v[0];
                            TxBuffer[2] = tempShortAddress.v[1];
                            TxBuffer[3] = associateStatus;
                            #if ADDITIONAL_NODE_ID_SIZE > 0
                                for(i = 0; i < ADDITIONAL_NODE_ID_SIZE; i++)
                                {
                                    TxBuffer[4+i] = AdditionalNodeID[i];
                                }
                            #endif
                            TxData = 4+ADDITIONAL_NODE_ID_SIZE;

                            #if defined(ENABLE_SECURITY)
                                IncomingFrameCounter[handle].Val = 0;
                                            #endif

                            #if defined(IEEE_802_15_4)
                                SendMACPacket(myPANID.v, ConnectionTable[handle].Address, PACKET_TYPE_COMMAND, 0);
                            #else
                                SendMACPacket(ConnectionTable[handle].Address, PACKET_TYPE_COMMAND);
                            #endif
                        }
                        break;
                    #endif

                    case MAC_COMMAND_ASSOCIATION_RESPONSE:
                        {
                            if(MACRxPacket.Payload[3] == ASSOCIATION_SUCCESSFUL)
                            {
                                //The join was successful
                                //assign myself the correct short address
                                myShortAddress.v[0] = MACRxPacket.Payload[1];
                                myShortAddress.v[1] = MACRxPacket.Payload[2];

                                #ifdef NWK_ROLE_COORDINATOR
                                    if(myShortAddress.v[0] == 0x00)
                                    {
                                        CONSOLE_PutString((char*)"I am a coordinator\r\n");
                                        role = ROLE_COORDINATOR;
                                        MiWiCapacityInfo.bits.Role = role;
                                        knownCoordinators |= ((1<<(myShortAddress.v[1] & 0x07)) + 1);
                                        //I know the PAN coordinator and myself
                                    }
                                    else
                                    {
                                        CONSOLE_PutString((char*)"I am an end device\r\n");
                                        role = ROLE_FFD_END_DEVICE;
                                        MiWiCapacityInfo.bits.Role = role;
                                    }
                                    #if defined(ENABLE_NVM)
                                        nvmPutRole(&role);
                                    #endif
                                #endif

                                //set the short address of the device
                                MiMAC_SetAltAddress(myShortAddress.v, myPANID.v);

                                //mark as having joined a network
                                MiWiStateMachine.bits.memberOfNetwork = 1;

                                //record the parents information
                                tempNodeStatus.Val = 0xBF;
                                for(i = 0; i < MY_ADDRESS_LENGTH; i++)
                                {
                                    tempLongAddress[i] = MACRxPacket.SourceAddress[i];
                                }

                                if(myShortAddress.v[0] == 0x00)
                                {
                                    //if I am a coordinator then my parent is the PAN coordinator
                                    //and I am a router
                                    tempShortAddress.Val = 0x0000;
                                }
                                else
                                {
                                    tempShortAddress.v[1] = myShortAddress.v[1];
                                    tempShortAddress.v[0] = 0x00;
                                }

                                tempPANID.Val = myPANID.Val;

                                //and add the parents information to the network table
                                myParent = AddNodeToNetworkTable();
                                #if defined(ENABLE_SECURITY)
                                                            IncomingFrameCounter[myParent].Val = 0;
                                                    #endif

                                                    #if ADDITIONAL_NODE_ID_SIZE > 0
                                                        for(i = 0; i < ADDITIONAL_NODE_ID_SIZE; i++)
                                                        {
                                                        ConnectionTable[myParent].PeerInfo[i] = MACRxPacket.Payload[4+i];
                                                    }
                                                    #endif

                                                    #if defined(ENABLE_NETWORK_FREEZER)
                                                        nvmPutMyPANID(myPANID.v);
                                                        nvmPutMyShortAddress(myShortAddress.v);
                                                        nvmPutMyParent(&myParent);
                                    nvmPutConnectionTableIndex(&(ConnectionTable[myParent]), myParent);
                                    #if defined(NWK_ROLE_COORDINATOR)
                                        nvmPutKnownCoordinators(&knownCoordinators);
                                    #endif
                                #endif

                                CONSOLE_PutString((char *)"\r\nJoin the network successfully\r\n");
                            }
                            else
                            {
                                //Access denied, remove this as my parent
                                myParent = 0xFF;
                                myPANID.Val = 0xFFFF;
                                tempShortAddress.Val = 0xFFFF;
                                MiMAC_SetAltAddress(tempShortAddress.v, myPANID.v);
                                #if defined(ENABLE_NETWORK_FREEZER)
                                    nvmPutMyParent(&myParent);
                                    nvmPutMyPANID(myPANID.v);
                                    nvmPutMyShortAddress(myShortAddress.v);
                                #endif
                            }
                        }
                        break;

                    #if !defined(TARGET_SMALL)
                        case MAC_COMMAND_DISASSOCIATION_NOTIFICATION:
                            {
                                uint8_t cIndex;

                                #if defined(IEEE_802_15_4)
                                    if( MACRxPacket.altSourceAddress )
                                    {
                                        tempShortAddress.v[0] = MACRxPacket.SourceAddress[0];
                                        tempShortAddress.v[1] = MACRxPacket.SourceAddress[1];

                                        if( (cIndex = SearchForShortAddress()) == 0xFF )
                                        {
                                            break;
                                        }
                                    }
                                    else
                                #endif
                                {
                                    for(i = 0; i < MY_ADDRESS_LENGTH; i++)
                                    {
                                        tempLongAddress[i] = MACRxPacket.SourceAddress[i];
                                    }
                                    if( (cIndex = SearchForLongAddress()) == 0xFF )
                                    {
                                        break;
                                    }
                                }

                                #if defined(NWK_ROLE_COORDINATOR)
                                    if( ConnectionTable[cIndex].status.bits.isFamily )
                                    {
                                        if( cIndex != myParent ) // it is from my child
                                        {
                                            ConnectionTable[cIndex].status.Val = 0;
                                            #if defined(ENABLE_NETWORK_FREEZER)
                                                nvmPutConnectionTableIndex(&(ConnectionTable[cIndex]), cIndex);
                                            #endif
                                        }
                                        else // it is from my parent
                                        {
                                            // notify my children
                                            for(i = 0; i < CONNECTION_SIZE; i++)
                                            {
                                                if( ConnectionTable[i].status.bits.isValid &&
                                                    ConnectionTable[i].status.bits.isFamily && (i != myParent ))
                                                {
                                                    uint16_t j;

                                                    MAC_FlushTx();
                                                    MiApp_WriteData(MAC_COMMAND_DISASSOCIATION_NOTIFICATION);
                                                    MTP.flags.Val = 0;
                                                    MTP.flags.bits.ackReq = 1;
                                                    MTP.flags.bits.packetType = PACKET_TYPE_COMMAND;
                                                    #if defined(IEEE_802_15_4)
                                                        MTP.altDestAddr = true;
                                                        MTP.altSrcAddr = true;
                                                        MTP.DestPANID.Val = ConnectionTable[i].PANID.Val;
                                                        MTP.DestAddress = ConnectionTable[i].AltAddress.v;
                                                    #else
                                                        MTP.flags.bits.sourcePrsnt = 1;
                                                        MTP.DestAddress = ConnectionTable[i].Address;
                                                    #endif
                                                    MiMAC_SendPacket(MTP, TxBuffer, TxData);
                                                    for(j = 0; j < 0xFFF; j++) {}   // delay
                                                }
                                                ConnectionTable[i].status.Val = 0;
                                            }
                                            myParent = 0xFF;
                                            myShortAddress.Val = 0xFFFF;
                                            myPANID.Val = 0xFFFF;
                                            MiMAC_SetAltAddress(myShortAddress.v, myPANID.v);
                                            MiWiStateMachine.bits.memberOfNetwork = 0;
                                            #if defined(ENABLE_NETWORK_FREEZER)
                                                nvmPutMyParent(&myParent);
                                                nvmPutMyShortAddress(myShortAddress.v);
                                                nvmPutMyPANID(myPANID.v);
                                                nvmPutConnectionTable(ConnectionTable);
                                            #endif
                                        }
                                    }
                                #else
                                    if( ConnectionTable[cIndex].status.bits.isFamily ) // it is from my parent
                                    {
                                        for(i = 0; i < CONNECTION_SIZE; i++)
                                        {
                                            ConnectionTable[i].status.Val = 0;
                                        }
                                        myParent = 0xFF;
                                        myShortAddress.Val = 0xFFFF;
                                        myPANID.Val = 0xFFFF;
                                        MiMAC_SetAltAddress(myShortAddress.v, myPANID.v);
                                        MiWiStateMachine.bits.memberOfNetwork = 0;
                                        #if defined(ENABLE_NETWORK_FREEZER)
                                            nvmPutMyParent(&myParent);
                                            nvmPutMyShortAddress(myShortAddress.v);
                                            nvmPutMyPANID(myPANID.v);
                                        #endif
                                    }
                                #endif

                            }
                            break;
                    #endif



                    #if defined(NWK_ROLE_COORDINATOR) && defined(ENABLE_INDIRECT_MESSAGE)
                    case MAC_COMMAND_DATA_REQUEST:
                    {
                        //uint8_t handle;

                        #if defined(IEEE_802_15_4)

                            if( MACRxPacket.altSourceAddress )
                            {
                                SendIndirectPacket(NULL, MACRxPacket.SourceAddress, true);
                            }
                            else
                            {
                                SendIndirectPacket(MACRxPacket.SourceAddress, NULL, false);
                            }

                        #else

                            SendIndirectPacket(MACRxPacket.SourceAddress, &(MACRxPacket.Payload[1]), true);

                        #endif

                        #if defined(ENABLE_ENHANCED_DATA_REQUEST)
                            #if defined(IEEE_802_15_4)
                                if( MACRxPacket.PayloadLen > 1 )
                                {
                                    goto HANDLE_DATA_PACKET;
                                }
                            #else

                                if( MACRxPacket.PayloadLen > 3 )
                                {
                                    for(i = 1; i < MACRxPacket.PayloadLen-2; i++)
                                    {
                                        MACRxPacket.Payload[i] = MACRxPacket.Payload[i+2];
                                    }
                                    MACRxPacket.PayloadLen -= 2;
                                    goto HANDLE_DATA_PACKET;
                                }
                            #endif
                        #endif


                        break;
                    }
                    #endif

                    #ifdef NWK_ROLE_COORDINATOR
                        case MAC_COMMAND_BEACON_REQUEST:
                            {
                                if( ConnMode > ENABLE_ACTIVE_SCAN_RSP )
                                {
                                    break;
                                }

                                //if we are a member of a network
                                if(MiWiStateMachine.bits.memberOfNetwork)
                                {
                                    if( MACRxPacket.Payload[1] != currentChannel )
                                    {
                                        break;
                                    }

                                    //send out a beacon as long as we are not
                                    //currently acting as an FFD end device
                                    if(role != ROLE_FFD_END_DEVICE)
                                    {
                                        // Patch nio - prevent beacon collision
                                        // no jitter for PAN_COORDINATOR
                                        if (role == ROLE_COORDINATOR)
                                        //#if !defined(TARGET_SMALL)
                                        {
                                            // static 20ms jitter
                                            // to let the PAN answer if
                                            // it's in vincinity
                                            uint8_t jitter = 20;
                                            MIWI_TICK t1, t2;
                                            while( jitter > 0 )
                                            {
                                                jitter--;
                                                t1 = MiWi_TickGet();
                                                while(1)
                                                {
                                                    t2 = MiWi_TickGet();
                                                    if( MiWi_TickGetDiff(t2, t1) > ONE_MILI_SECOND )
                                                    {
                                                        break;
                                                    }
                                                }
                                            }
                                            // + random jitters
                                            // if another coordinator wants to
                                            // answer
                                            BroadcastJitter(20);
                                            BroadcastJitter(20);
                                            BroadcastJitter(20);
                                        }
                                        //#endif
                                        SendBeacon();
                                    }
                                }
                            }
                            break;
                    #endif


                    #if defined(ENABLE_TIME_SYNC) && defined(ENABLE_SLEEP)
                        case MAC_COMMAND_TIME_SYNC_DATA_PACKET:
                        case MAC_COMMAND_TIME_SYNC_COMMAND_PACKET:
                            {
                                WakeupTimes.v[0] = MACRxPacket.Payload[1];
                                WakeupTimes.v[1] = MACRxPacket.Payload[2];
                                CounterValue.v[0] = MACRxPacket.Payload[3];
                                CounterValue.v[1] = MACRxPacket.Payload[4];

                                if( MACRxPacket.PayloadLen > 5 )
                                {
                                    if( MACRxPacket.Payload[0] == MAC_COMMAND_TIME_SYNC_DATA_PACKET )
                                    {
                                        for(i = 0; i < MACRxPacket.PayloadLen-5; i++)
                                        {
                                            MACRxPacket.Payload[i] = MACRxPacket.Payload[5+i];
                                        }
                                        MACRxPacket.PayloadLen -= 5;

                                        goto HANDLE_DATA_PACKET;
                                    }
                                    else
                                    {
                                        for(i = 0; i < MACRxPacket.PayloadLen-5; i++)
                                        {
                                            MACRxPacket.Payload[i] = MACRxPacket.Payload[5+i];
                                        }
                                        MACRxPacket.PayloadLen -= 5;

                                        goto HANDLE_COMMAND_PACKET;
                                    }
                                }
                                else
                                {
                                    MiWiStateMachine.bits.DataRequesting = 0;
                                }
                            }
                            break;
                    #endif

                    default:
                        break;
                  }
                break;

            default:
                break;

        }

        if( MiWiStateMachine.bits.RxHasUserData == 0 )
        {
            MiMAC_DiscardPacket();
        }
    }

    t1 = MiWi_TickGet();

    //if there really isn't anything going on
    #if defined(NWK_ROLE_COORDINATOR) && defined(ENABLE_INDIRECT_MESSAGE)
        // check indirect message periodically. If an indirect message is not acquired within
        // time of INDIRECT_MESSAGE_TIMEOUT
        for(i = 0; i < INDIRECT_MESSAGE_SIZE; i++)
        {
            if( indirectMessages[i].flags.bits.isValid )
            {
                if( MiWi_TickGetDiff(t1, indirectMessages[i].TickStart) > INDIRECT_MESSAGE_TIMEOUT )
                {
                    indirectMessages[i].flags.Val = 0x00;
                }
            }
        }
    #endif //COORDINATOR_CAPABLE


    #if defined(ENABLE_SLEEP)
        //if we are an RFD and a member of the network
        if(MiWiStateMachine.bits.memberOfNetwork)
        {
            if(MiWiStateMachine.bits.DataRequesting)
            {
                t2.Val = MiWi_TickGetDiff(t1, DataRequestTimer);
                if(t2.Val > RFD_DATA_WAIT)
                {
                    MiWiStateMachine.bits.DataRequesting = 0;
                    #if defined(ENABLE_TIME_SYNC)
                        WakeupTimes.Val = RFD_WAKEUP_INTERVAL / 16;
                        CounterValue.Val = 0xFFFF - ((uint16_t)4000*(RFD_WAKEUP_INTERVAL % 16));
                    #endif
                }
            }
        }
    #endif

    #if defined(ENABLE_TIME_SYNC) && !defined(ENABLE_SLEEP) && defined(ENABLE_INDIRECT_MESSAGE)
        if( MiWi_TickGetDiff(t1, TimeSyncTick) > ((ONE_SECOND) * RFD_WAKEUP_INTERVAL) )
        {
            TimeSyncTick.Val += ((uint32_t)(ONE_SECOND) * RFD_WAKEUP_INTERVAL);
            if( TimeSyncTick.Val > t1.Val )
            {
                TimeSyncTick.Val = t1.Val;
            }
            TimeSyncSlot = 0;
        }
    #endif


    #if defined(ENABLE_NETWORK_FREEZER) && defined(NWK_ROLE_COORDINATOR)
        if( MiWiStateMachine.bits.saveConnection )
        {
            if(  MiWi_TickGetDiff(t1, nvmDelayTick) > (ONE_SECOND) )
            {
                MiWiStateMachine.bits.saveConnection = 0;
                nvmPutKnownCoordinators(&knownCoordinators);
                nvmPutRoutingTable(RoutingTable);
                #if !defined(IEEE_802_15_4)
                    nvmPutConnectionTable(ConnectionTable);
                #endif
            }
        }
    #endif

    #if !defined(ENABLE_SLEEP)
        for(i = 0; i < BROADCAST_RECORD_SIZE; i++)
        {
            if( BroadcastRecords[i].RxCounter > 0 )
            {
                if( MiWi_TickGetDiff(t1, BroadcastRecords[i].StartTick) > BROADCAST_RECORD_TIMEOUT )
                {
                    BroadcastRecords[i].RxCounter = 0;
                }
            }
        }
    #endif

    //clean up an old socket if one still exists
    if(openSocketInfo.status.bits.requestIsOpen)
    {
        if(openSocketInfo.status.bits.matchFound)
        {
            #ifdef NWK_ROLE_COORDINATOR
                uint8_t j;

                CONSOLE_PutString((char*)"sending out second response\r\n");

                MiApp_FlushTx();
                TxBuffer[TxData++] = MIWI_STACK_REPORT_TYPE;      //Report Type
                TxBuffer[TxData++] = OPEN_SOCKET_RESPONSE;      //Report ID


                //copy the long and short address from the Rx Buffer
                for(j=0;j<MY_ADDRESS_LENGTH;j++)
                {
                    TxBuffer[TxData++] = openSocketInfo.LongAddress1[j];
                }

                TxBuffer[TxData++] = openSocketInfo.ShortAddress1.v[0];
                TxBuffer[TxData++] = openSocketInfo.ShortAddress1.v[1];

                #if ADDITIONAL_NODE_ID_SIZE > 0
                    for(j = 0; j < ADDITIONAL_NODE_ID_SIZE; j++)
                    {
                        TxBuffer[TxData++] = openSocketInfo.AdditionalNodeID1[j];
                    }
                #endif

               //MiApp_UnicastAddress(openSocketInfo.ShortAddress2.v, false, false);
                    UnicastShortAddress(openSocketInfo.ShortAddress2.v);
                openSocketInfo.status.bits.requestIsOpen = 0;
            #endif

            //openSocketInfo.status.bits.requestIsOpen = 0;
        }
        else
        {
            t2.Val = MiWi_TickGetDiff(t1, openSocketInfo.socketStart);

            if(t2.Val > OPEN_SOCKET_TIMEOUT)
            {
                //invalidate the expired socket request
                openSocketInfo.status.bits.requestIsOpen = 0;
            }
        }
    }
}


#ifdef NWK_ROLE_COORDINATOR
    /*********************************************************************
     * Function:        bool RouteMessage(API_UINT16_UNION PANID,
     *                                    API_UINT16_UNION ShortAddress, bool SecEn)
     *
     * PreCondition:    Coordinator has joined the network
     *
     * Input:           PANID           - PAN identifier of the destination
     *                                    node
     *                  ShortAddress    - Network short address of the
     *                                    destination node
     *                  SecEn           - Boolean to indicate if the message
     *                                    payload needs to be secured
     *
     * Output:          A boolean to indicate if routing successful
     *
     * Side Effects:    None
     *
     * Overview:        This function is the backbone of MiWi routing
     *                  mechanism. MiWi use this function to route
     *                  the message across multiple hops to reach the
     *                  destination node.
     ********************************************************************/
    bool RouteMessage(API_UINT16_UNION PANID, API_UINT16_UNION ShortAddress, bool SecEn)
    {
        uint8_t parentNode = (ShortAddress.v[1] & 0x07);
        uint8_t i;

        if( parentNode == myShortAddress.v[1] )
        {
            // destination is my child
            if( ShortAddress.v[0] > 0x80 )
            {
                #if defined(ENABLE_INDIRECT_MESSAGE)
                    // this is a sleeping device, need indirect message
                    #if defined(IEEE_802_15_4)
                        return SaveIndirectMessage(false, PANID, ShortAddress.v, true, SecEn);
                    #else
                        tempShortAddress.Val = ShortAddress.Val;
                        if( (i = SearchForShortAddress()) == 0xFF )
                        {
                            return SaveIndirectMessage(false, ShortAddress.v, true, SecEn);
                        }

                        return SaveIndirectMessage(false, ConnectionTable[i].Address, false, SecEn);
                    #endif
                #else
                    return false;
                #endif
            }
            else
            {
                MTP.flags.Val = 0;
                MTP.flags.bits.ackReq = 1;
                MTP.flags.bits.secEn = SecEn;

                tempShortAddress.Val = ShortAddress.Val;

                #if defined(IEEE_802_15_4)
                    MTP.altDestAddr = true;
                    MTP.altSrcAddr = true;
                    MTP.DestAddress = tempShortAddress.v;
                    MTP.DestPANID.Val = myPANID.Val;
                #else
                    if( (i = SearchForShortAddress()) != 0xFF )
                    {
                        MTP.DestAddress = ConnectionTable[i].Address;
                    }
                    else
                    {
                        // the children's info is not in the connection table
                        // should not happen
                        return false;
                    }
                #endif
                return MiMAC_SendPacket(MTP, TxBuffer, TxData);
            }
        }

        if( (knownCoordinators & (1 << parentNode) ) > 0 )
        {
            if( RouterFailures[parentNode] >= MAX_ROUTING_FAILURE )
            {
                RouterFailures[parentNode] = 0;
                knownCoordinators &= ((1<<parentNode) ^ 0xFF);
                RoutingTable[parentNode] = 0;
                #if defined(ENABLE_NETWORK_FREEZER)
                    nvmPutKnownCoordinators(&knownCoordinators);
                    nvmPutRoutingTable(RoutingTable);
                #endif
                SendBeacon();
                return false;
            }
            else
            {
                // we know the destination's parent directly
                MTP.flags.Val = 0;
                MTP.flags.bits.ackReq = 1;
                MTP.flags.bits.secEn = SecEn;
                tempShortAddress.v[0] = 0;
                tempShortAddress.v[1] = parentNode;

                #if defined(IEEE_802_15_4)
                    MTP.altDestAddr = true;
                    MTP.altSrcAddr = true;
                    MTP.DestAddress = tempShortAddress.v;
                    MTP.DestPANID.Val = myPANID.Val;
                #else
                    if( (i = SearchForShortAddress()) != 0xFF )
                    {
                        MTP.DestAddress = ConnectionTable[i].Address;
                    }
                    else
                    {
                        // highly impossible for none 15.4, where the
                        // access of Coordinators not through beacon
                        goto ROUTE_THROUGH_NEIGHBOR;
                    }
                #endif
                if( MiMAC_SendPacket(MTP, TxBuffer, TxData) == false )
                {
                    RouterFailures[parentNode]++;
                    return false;
                }
                else
                {
                    RouterFailures[parentNode] = 0;
                    return true;
                }
            }
        }

ROUTE_THROUGH_NEIGHBOR: 
        for(i = 0; i < 8; i++)
        {
            if( (RoutingTable[i] & (1 << parentNode) ) > 0 )
            {
                if( RouterFailures[i] >= MAX_ROUTING_FAILURE )
                {
                    RouterFailures[i] = 0;
                    knownCoordinators &= ((1<<i) ^ 0xFF);
                    RoutingTable[i] = 0;
                    #if defined(ENABLE_NETWORK_FREEZER)
                        nvmPutKnownCoordinators(&knownCoordinators);
                        nvmPutRoutingTable(RoutingTable);
                    #endif
                    if( role != ROLE_FFD_END_DEVICE )
                    {
                        SendBeacon();
                    }
                    else
                    {
                        // send out beacon request
                        MAC_FlushTx();
                        MiApp_WriteData(MAC_COMMAND_BEACON_REQUEST);
                        MiApp_WriteData(currentChannel);
                        #if defined(IEEE_802_15_4)
                            tempPANID.Val = 0xFFFF;
                            SendMACPacket(tempPANID.v, NULL, PACKET_TYPE_COMMAND, 0);
                        #else
                            SendMACPacket(NULL, PACKET_TYPE_COMMAND);
                        #endif
                    }
                    return false;
                }
                else
                {
                    // we know the destination's neighbor directly
                    MTP.flags.Val = 0;
                    MTP.flags.bits.ackReq = 1;
                    MTP.flags.bits.secEn = SecEn;
                    tempShortAddress.v[0] = 0;
                    tempShortAddress.v[1] = i;

                    #if defined(IEEE_802_15_4)
                        MTP.altDestAddr = true;
                        MTP.altSrcAddr = true;
                        MTP.DestAddress = tempShortAddress.v;
                        MTP.DestPANID.Val = myPANID.Val;
                    #else
                        if( (i = SearchForShortAddress()) != 0xFF )
                        {
                            MTP.DestAddress = ConnectionTable[i].Address;
                        }
                        else
                        {
                            // highly impossible for none 15.4, where the
                            // access of Coordinators not through beacon
                            goto ROUTE_THROUGH_TREE;
                        }
                    #endif
                    if( MiMAC_SendPacket(MTP, TxBuffer, TxData) == false )
                    {
                        RouterFailures[i]++;
                        return false;
                    }
                    RouterFailures[i] = 0;
                    return true;
                }
            }
        }

ROUTE_THROUGH_TREE:
        if( role != ROLE_PAN_COORDINATOR )
        {
            MTP.flags.Val = 0;
            MTP.flags.bits.ackReq = 1;
            MTP.flags.bits.secEn = SecEn;

            if( role == ROLE_COORDINATOR)
            {
                #if defined(IEEE_802_15_4)
                    tempShortAddress.Val = 0;
                #else
                    for(i = 0; i < MY_ADDRESS_LENGTH; i++)
                    {
                        tempLongAddress[i] = ConnectionTable[myParent].Address[i];
                    }
                #endif
            }
            else
            {
                for(i = 0; i < 8; i++)
                {
                    if( knownCoordinators && (0x01 << i) )
                    {
                        break;
                    }
                }
                if( i < 8 )
                {
                    tempShortAddress.v[1] = i;
                    tempShortAddress.v[0] = 0;
                }
                else
                {
                    // we have tried all possible way, just try to send to PAN as the last try
                    tempShortAddress.Val = 0;
                }

                #if !defined(IEEE_802_15_4)
                    {
                        uint8_t j;

                        if( (j = SearchForShortAddress()) < CONNECTION_SIZE )
                        {
                            for(i = 0; i < MY_ADDRESS_LENGTH; i++)
                            {
                                tempLongAddress[i] = ConnectionTable[j].Address[i];
                            }
                        }
                        else
                        {
                            for(i = 0; i < MY_ADDRESS_LENGTH; i++)
                            {
                                tempLongAddress[i] = ConnectionTable[myParent].Address[i];
                            }
                        }
                    }
                #endif

            }

            #if defined(IEEE_802_15_4)
                MTP.altDestAddr = true;
                MTP.altSrcAddr = true;
                MTP.DestAddress = tempShortAddress.v;        // send to the PAN Coordinator
                MTP.DestPANID.Val = myPANID.Val;
            #else
                MTP.DestAddress = ConnectionTable[myParent].Address;
            #endif

            if( MiMAC_SendPacket(MTP, TxBuffer, TxData) == false )
            {
                RouterFailures[0]++;
                return false;
            }
            RouterFailures[0] = 0;
            return true;
        }

        // Highly unlikely to get here, a PAN Coordinator should have all Coordinator on its
        // neighbor table, here just as the backup plan for extreme case
        MTP.flags.Val = 0;
        MTP.flags.bits.ackReq = 1;
        MTP.flags.bits.secEn = SecEn;

        tempShortAddress.v[1] = parentNode;
        tempShortAddress.v[0] = 0;

        #if defined(IEEE_802_15_4)
            MTP.altDestAddr = true;
            MTP.altSrcAddr = true;
            MTP.DestAddress = tempShortAddress.v;
            MTP.DestPANID.Val = myPANID.Val;
        #else
            MTP.DestAddress = ConnectionTable[myParent].Address;
        #endif

        if( MiMAC_SendPacket(MTP, TxBuffer, TxData) == false )
        {
            RouterFailures[0]++;
            return false;
        }
        RouterFailures[0] = 0;
        return true;

    }
#endif




/*********************************************************************
 * Function:        bool SendMACPacket(uint8_t *PANID, uint8_t *Address,
 *                                     uint8_t PacketType, uint8_t ModeMask)
 *
 * PreCondition:    Transceiver has been initialized properly
 *
 * Input:           PANID           - PAN identifier of the destination
 *                                    node. (IEEE 802.15.4 only)
 *                  Address         - Address of the destination node.
 *                                    Always long address for non-IEEE
 *                                    802.15.4, can be short or long
 *                                    address for IEEE 802.15.4.
 *                  PacketType      - The packet type, passed to
 *                                    transceiver driver directly
 *                  ModeMask        - The source and destination address
 *                                    mode (short or long) maks.
 *                                    (IEEE 802.15.4 only)
 *
 * Output:          A boolean to indicate if packet sent successfully
 *
 * Side Effects:    None
 *
 * Overview:        This function is a bridge from MiWi layer to
 *                  transceiver MAC layer. It organizes the MiMAC
 *                  layer parameters and return  the status of
 *                  MiMAC transmission status.
 ********************************************************************/
#if defined(IEEE_802_15_4)
    bool SendMACPacket(uint8_t *PANID, uint8_t *Address, uint8_t PacketType, uint8_t ModeMask)
#else
    bool SendMACPacket(uint8_t *Address, uint8_t PacketType)
#endif
{   
    MTP.flags.Val = 0;

    MTP.flags.bits.packetType = PacketType;
    if( Address == NULL )
    {
        MTP.flags.bits.broadcast = 1;
    }
    MTP.flags.bits.ackReq = (MTP.flags.bits.broadcast) ? 0:1;
    MTP.flags.bits.sourcePrsnt = 1;

    MTP.DestAddress = Address;

    #if defined(IEEE_802_15_4)
        if( (ModeMask & MSK_ALT_DST_ADDR) > 0)
        {
            MTP.altDestAddr = true;
        }
        else
        {
            MTP.altDestAddr = false;
        }
        if( (ModeMask & MSK_ALT_SRC_ADDR) > 0)
        {
            MTP.altSrcAddr = true;
        }
        else
        {
            MTP.altSrcAddr = false;
        }
        MTP.DestPANID.v[0] = PANID[0];
        MTP.DestPANID.v[1] = PANID[1];
    #endif

    return MiMAC_SendPacket(MTP, TxBuffer, TxData);
}
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
