nio101/MUTA_units/src/18F27J53_op_basecamp/dev_18F27J53_operator_basecamp.X/src/18F27J53/spi.c

/********************************************************************
 Software License Agreement:

 The software supplied herewith by Microchip Technology Incorporated
 (the "Company") for its PIC(R) Microcontroller is intended and
 supplied to you, the Company's customer, for use solely and
 exclusively on Microchip PIC Microcontroller products. The
 software is owned by the Company and/or its supplier, and is
 protected under applicable copyright laws. All rights are reserved.
 Any use in violation of the foregoing restrictions may subject the
 user to criminal sanctions under applicable laws, as well as to
 civil liability for the breach of the terms and conditions of this
 license.

 THIS SOFTWARE IS PROVIDED IN AN "AS IS" CONDITION. NO WARRANTIES,
 WHETHER EXPRESS, IMPLIED OR STATUTORY, INCLUDING, BUT NOT LIMITED
 TO, IMPLIED WARRANTIES OF MERCHANTABILITY AND FITNESS FOR A
 PARTICULAR PURPOSE APPLY TO THIS SOFTWARE. THE COMPANY SHALL NOT,
 IN ANY CIRCUMSTANCES, BE LIABLE FOR SPECIAL, INCIDENTAL OR
 CONSEQUENTIAL DAMAGES, FOR ANY REASON WHATSOEVER.
 *******************************************************************/

/************************ HEADERS **********************************/

#include "system.h"
#include "system_config.h"



/*********************************************************************
* Function:         void SPIPut(uint8_t v)
*
* PreCondition:     SPI has been configured
*
* Input:		    v - is the byte that needs to be transfered
*
* Output:		    none
*
* Side Effects:	    SPI transmits the byte
*
* Overview:		    This function will send a byte over the SPI
*
* Note:			    None
********************************************************************/
 void SPIPut(uint8_t v)
{
    
    // mod NIO: redirect SPI to SPI2
    // since MSSP1 is used for I2C

    #if !defined(HARDWARE_SPI)
    {
        uint8_t i;
        SPI_SDO = 0;
        SPI_SCK = 0;

        for(i = 0; i < 8; i++)
        {
            SPI_SDO = (v >> (7-i));
            SPI_SCK = 1;
            SPI_SCK = 0;
        }
        SPI_SDO = 0;
    }
    #else
    {
      
        uint8_t i;
        
        PIR3bits.SSP2IF = 0;
        //clear SSP2BUF
        i = SSP2BUF;

        do
        {
            SSP2CON1bits.WCOL = 0;
            SSP2BUF = v;
        } while( SSP2CON1bits.WCOL );

        while( PIR3bits.SSP2IF == 0 );

        PIR3bits.SSP2IF = 0;
        
    }
    #endif
}


/*********************************************************************
* Function:         uint8_t SPIGet(void)
*
* PreCondition:     SPI has been configured
*
* Input:		    none
*
* Output:		    uint8_t - the byte that was last received by the SPI
*
* Side Effects:	    none
*
* Overview:		    This function will read a byte over the SPI
*
* Note:			    None
********************************************************************/
uint8_t SPIGet(void)
{

    // mod NIO: redirect SPI to SPI2
    // since MSSP1 is used for I2C

    #if !defined(HARDWARE_SPI)
        uint8_t i;
        uint8_t spidata = 0;


        SPI_SDO = 0;
        SPI_SCK = 0;

        for(i = 0; i < 8; i++)
        {

            spidata = (spidata << 1) | SPI_SDI;
            SPI_SCK = 1;
            SPI_SCK = 0;
        }

        return spidata;
    #else
        SPIPut(0x00);
        return SSP2BUF;
    #endif
}

#if defined(SUPPORT_TWO_SPI)
        /*********************************************************************
        * Function:         void SPIPut2(uint8_t v)
        *
        * PreCondition:     SPI has been configured
        *
        * Input:		    v - is the byte that needs to be transfered
        *
        * Output:		    none
        *
        * Side Effects:	    SPI transmits the byte
        *
        * Overview:		    This function will send a byte over the SPI
        *
        * Note:			    None
        ********************************************************************/
         void SPIPut2(uint8_t v)
        {
            

            #if !defined(HARDWARE_SPI)
            {
                uint8_t i;
                
                SPI_SDO2 = 0;
                SPI_SCK2 = 0;

                for(i = 0; i < 8; i++)
                {
                    SPI_SDO2 = (v >> (7-i));
                    SPI_SCK2 = 1;
                    SPI_SCK2 = 0;
                }
                SPI_SDO2 = 0;
            }
            #else

            {
                uint8_t i;
                //Reset the interrupt pin
                
                PIR3bits.SSP2IF = 0;
                i = SSP2BUF;
                
                do
                {
                    
                    SSP2CON1bits.WCOL = 0;
            		//Reset write collision bit
                    
                    SSP2BUF = v;
            		//load the buffer
                
                } while( SSP2CON1bits.WCOL );

            	//perform write again if write collision occurs
                
                while( PIR3bits.SSP2IF == 0 );

            	//Wait until interrupt is received from the MSSP module
            	
            	PIR3bits.SSP2IF = 0;
            	//Reset the interrupt
            }
            #endif
        }

        /*********************************************************************
        * Function:         uint8_t SPIGet2(void)
        *
        * PreCondition:     SPI has been configured
        *
        * Input:		    none
        *
        * Output:		    uint8_t - the byte that was last received by the SPI
        *
        * Side Effects:	    none
        *
        * Overview:		    This function will read a byte over the SPI
        *
        * Note:			    None
        ********************************************************************/
        uint8_t SPIGet2(void)
        {
            #if !defined(HARDWARE_SPI)
                uint8_t i;
                uint8_t spidata = 0;


                SPI_SDO2 = 0;
                SPI_SCK2 = 0;

                for(i = 0; i < 8; i++)
                {
                    spidata = (spidata << 1) | SPI_SDI2;
                    SPI_SCK2 = 1;
                    SPI_SCK2 = 0;
                }

                return spidata;
            #else

                SPIPut2(0x00);
                return SSP2BUF;
            #endif
        }
    #endif
